TobiasVanDyk/Microdexed-Synth-Variations/i2cbackpack/address-jumpers.png

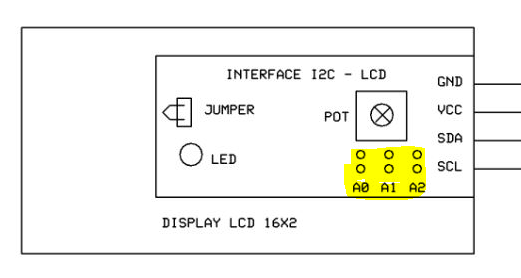
i2cbackpack/address-jumpers.png
