TobiasVanDyk/Microdexed-Synth-Variations/Microdexed2/images/mdt2.jpg

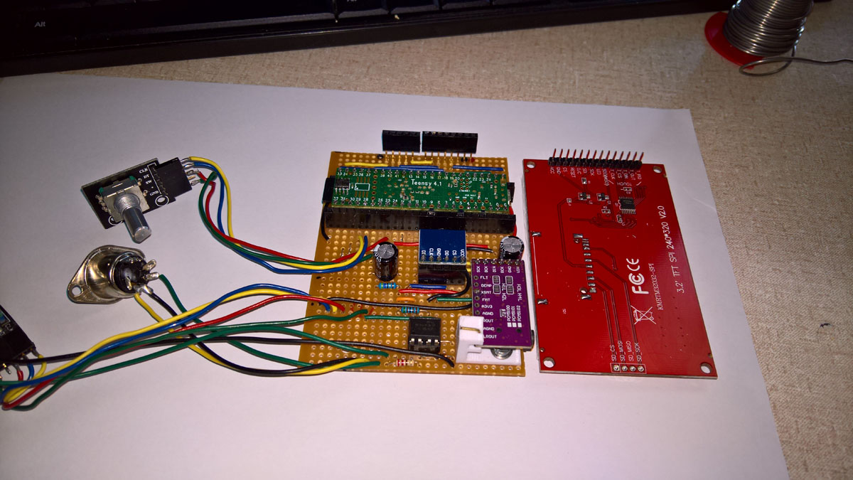
Microdexed2/images/mdt2.jpg
