TobiasVanDyk/Microdexed-Synth-Variations/Microdexed3/images/SDCard.png

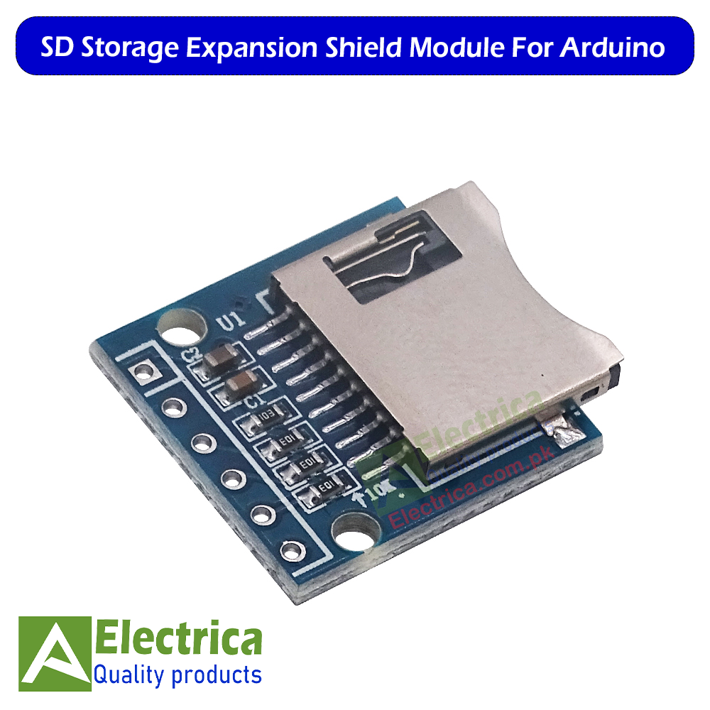
Microdexed3/images/SDCard.png
