TobiasVanDyk/Microdexed-Synth-Variations/Microdexed3/images/SDCardBack.png

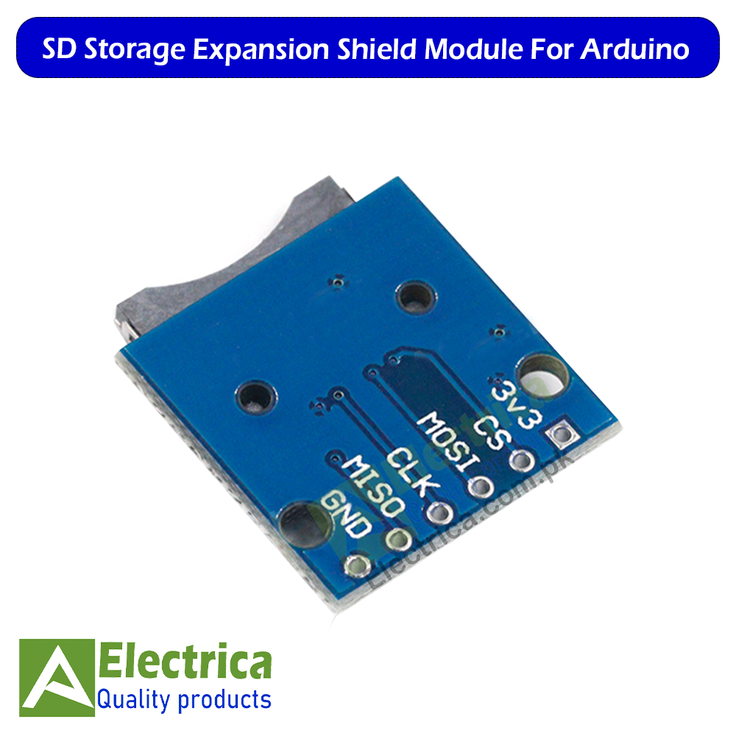
Microdexed3/images/SDCardBack.png
