TobiasVanDyk/Microdexed-Synth-Variations/Minidexed1/images/Pins.png

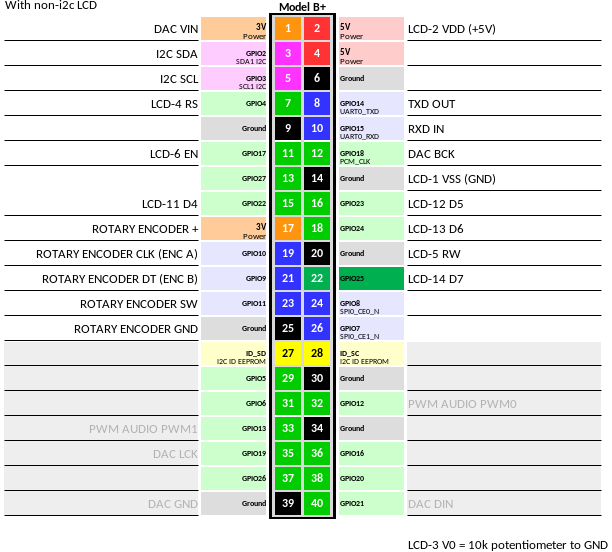
Minidexed1/images/Pins.png
