TobiasVanDyk/Microdexed-Synth-Variations/Minidexed2/Encoder.JPG

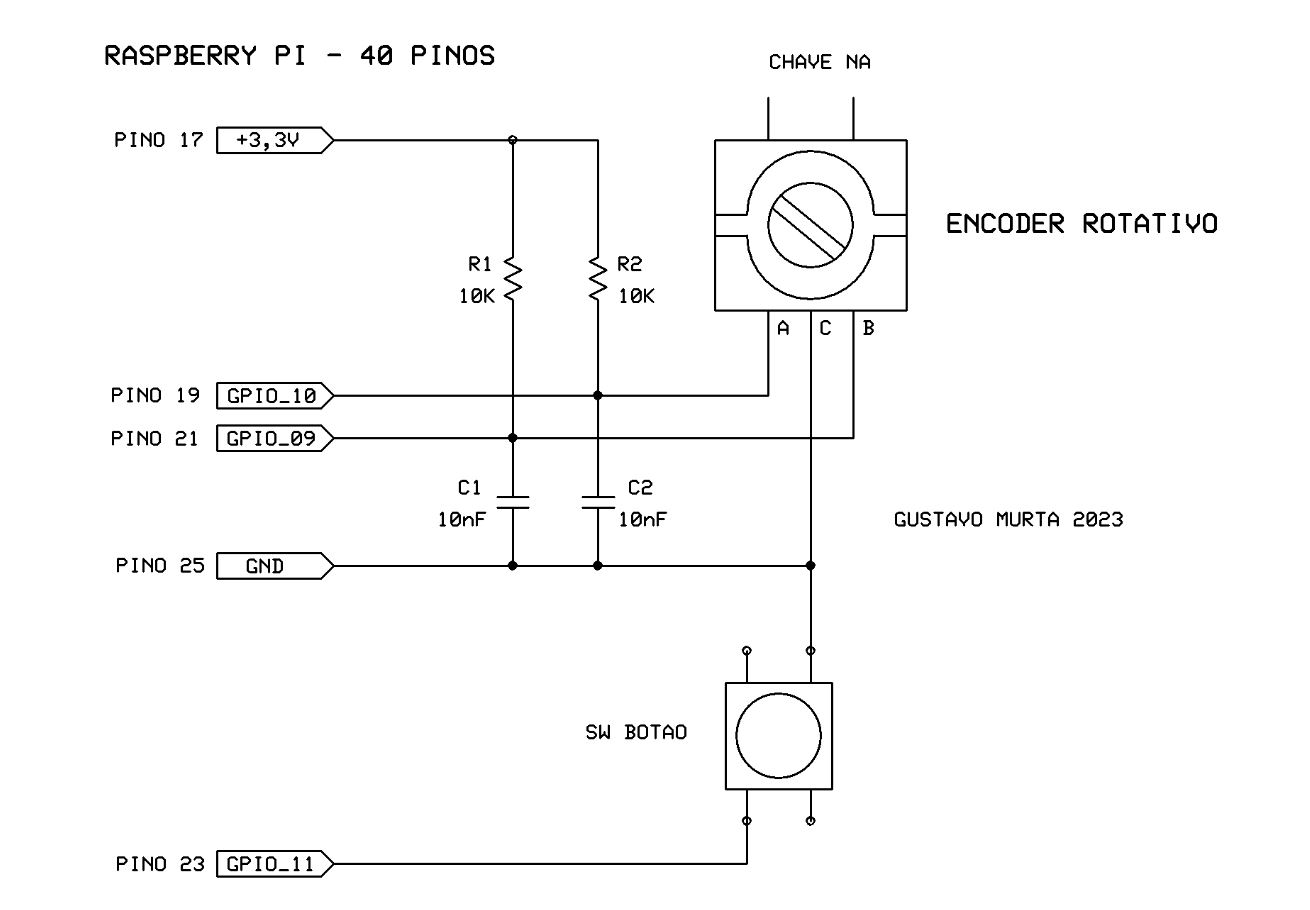
Minidexed2/Encoder.JPG
