TobiasVanDyk/Microdexed-Synth-Variations/Minidexed1/Minidexed-compile-WSL2-Win11/minidexed.ini

#
# minidexed.ini
#

# Sound device
SoundDevice=i2s
#SoundDevice=pwm
#SoundDevice=hdmi
SampleRate=48000
#ChunkSize=256
DACI2CAddress=0
ChannelsSwapped=0
# Engine Type ( 1=Modern ; 2=Mark I ; 3=OPL )
EngineType=1

# MIDI
MIDIBaudRate=31250
#MIDIThru=umidi1,ttyS1
IgnoreAllNotesOff=0
MIDIAutoVoiceDumpOnPC=1
HeaderlessSysExVoices=0
# Program Change enable
#   0 = Ignore all Program Change messages.
#   1 = Respond to Program Change messages.
MIDIRXProgramChange=1
# Program Change mode
#   0 = Only recognise Program Change 0-31.
#   1 = Support 0-127 across four consecutive banks.
# NB: Only relevant if PerformanceSelectChannel=0
ExpandPCAcrossBanks=1
# Program Change action:
#   0 = Program Change messages select voices on the channel associated with each TG.
#   1-16 = Program Change messages on this channel select performances.
#   >16 = Program Change messages on ANY channel select performances.
# NB: In performance mode, all Program Change messages on other channels are ignored.
PerformanceSelectChannel=0

# HD44780 LCD
LCDEnabled=1
LCDPinEnable=17
LCDPinRegisterSelect=4
LCDPinReadWrite=0
LCDPinData4=22
LCDPinData5=23
LCDPinData6=24
LCDPinData7=25
LCDI2CAddress=0x27

# SSD1306 LCD
# For a 128x32 display, set LCDColumns=20; LCDRows=2
# For a 128x64 display, set LCDColumns=20; LCDRows=4
SSD1306LCDI2CAddress=0x0
SSD1306LCDWidth=128
SSD1306LCDHeight=32
SSD1306LCDRotate=0
SSD1306LCDMirror=0

# Default is 16x2 display (e.g. HD44780)
LCDColumns=16
LCDRows=2

# GPIO Button Navigation
#  Any buttons set to 0 will be ignored
ButtonPinPrev=0
ButtonActionPrev=
ButtonPinNext=0
ButtonActionNext=
ButtonPinBack=11
ButtonActionBack=longpress
ButtonPinSelect=11
ButtonActionSelect=click
ButtonPinHome=11
ButtonActionHome=doubleclick
ButtonPinShortcut=11
# (Shortcut doesn't have an action)

# GPIO Program/TG Selection
#  Any buttons set to 0 will be ignored
ButtonPinPgmUp=0
ButtonActionPgmUp=
ButtonPinPgmDown=0
ButtonActionPgmDown=
ButtonPinTGUp=0
ButtonActionTGUp=
ButtonPinTGDown=0
ButtonActionTGDown=

# Timeouts in milliseconds for double click and long press
DoubleClickTimeout=400
LongPressTimeout=400

# MIDI Button Navigation
#  Specify MIDI CC to act as a button (0 = ununsed, so don't use CC 0)
#  NB: Off < 64 < ON
# CC channel: 0=OFF; 1-16 MIDI Ch; >16 Omni
# If MIDIButtonNotes>0 then treat MIDIButton numbers as MIDI
# Note numbers, triggered with NoteOn/NoteOff, not CC numbers.
MIDIButtonCh=0
MIDIButtonNotes=0
MIDIButtonPrev=0
MIDIButtonNext=0
MIDIButtonBack=0
MIDIButtonSelect=0
MIDIButtonHome=0
MIDIButtonPgmUp=0
MIDIButtonPgmDown=0
MIDIButtonTGUp=0
MIDIButtonTGDown=0

# KY-040 Rotary Encoder
EncoderEnabled=1
EncoderPinClock=10
EncoderPinData=9

# Debug
MIDIDumpEnabled=0
ProfileEnabled=0

# Performance
PerformanceSelectToLoad=1
