TobiasVanDyk/Microdexed-Synth-Variations/Microdexed3/MicroDexedTeensy41Dev/UI.hpp

/*
   MicroDexed

   MicroDexed is a port of the Dexed sound engine
   (https://github.com/asb2m10/dexed) for the Teensy-3.5/3.6/4.x with audio shield.
   Dexed ist heavily based on https://github.com/google/music-synthesizer-for-android

   (c)2018-2023 H. Wirtz <wirtz@parasitstudio.de>
   (c)2021-2022 H. Wirtz <wirtz@parasitstudio.de>, M. Koslowski <positionhigh@gmx.de>

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
   You should have received a copy of the GNU General Public License
   along with this program; if not, write to the Free Software Foundation,
   Inc., 51 Franklin Street, Fifth Floor, Boston, MA 02110-1301  USA
*/

#pragma once

#include "config.h"
#include <LCDMenuLib2.h>
#include <MD_REncoder.h>
#include <effect_modulated_delay.h>
#include <effect_stereo_mono.h>
#include <effect_mono_stereo.h>
#include <effect_platervbstereo.h>
#include <template_mixer.hpp>
#include "disp_plus.h"
#include "midi_devices.hpp"
#include "synth_dexed.h"
#include "synth_mda_epiano.h"
#include "drumset.h"
#include "dexed_sd.h"
#include <effect_stereo_panorama.h>
#if defined(USE_DELAY_8M)
#include <effect_delay_ext8.h>
#endif

#define _LCDML_DISP_cols LCD_cols
#define _LCDML_DISP_rows LCD_rows

#ifdef I2C_DISPLAY
#define _LCDML_DISP_cfg_cursor 0x7E  // cursor Symbol
#else
#define _LCDML_DISP_cfg_cursor 0x8d  // cursor Symbol
#endif
#define _LCDML_DISP_cfg_scrollbar 1  // enable a scrollbar

extern uint8_t midi_learn_mode;
extern uint8_t active_sample;

extern config_t configuration;
extern void set_volume(uint8_t v, uint8_t m);
extern bool load_sysex(uint8_t b, uint8_t v);
extern void generate_version_string(char* buffer, uint8_t len);
extern void _softRestart(void);
extern float midi_volume_transform(uint8_t midi_amp);
extern float volume_transform(float amp);
extern uint8_t selected_instance_id;
extern char receive_bank_filename[FILENAME_LEN];
extern void eeprom_update(void);

#if NUM_DRUMS > 0
#include "midinotes.h"
#include "drumset.h"
extern void get_sd_performance_name_json(uint8_t number, char* name, uint8_t len);
extern bool save_sd_performance_json(uint8_t p);
extern uint8_t drum_midi_channel;
uint8_t activesample = 0;
#endif

#ifdef SGTL5000_AUDIO_ENHANCE
#include "control_sgtl5000plus.h"
extern AudioControlSGTL5000Plus sgtl5000;
#else
extern AudioControlSGTL5000 sgtl5000;
#endif

extern AudioSynthDexed* MicroDexed[NUM_DEXED];

extern AudioSynthWaveform* chorus_modulator[NUM_DEXED];
extern AudioEffectModulatedDelay* modchorus[NUM_DEXED];
extern AudioMixer<2>* chorus_mixer[NUM_DEXED];
extern AudioMixer<2>* delay_fb_mixer[NUM_DEXED];
#if defined(USE_DELAY_8M)
extern AudioEffectDelayExternal8* delay_fx[NUM_DEXED];
#else
extern AudioEffectDelay* delay_fx[NUM_DEXED];
#endif
extern AudioMixer<2>* delay_mixer[NUM_DEXED];
extern AudioEffectMonoStereo* mono2stereo[NUM_DEXED];
extern AudioMixer<2> microdexed_peak_mixer;
extern AudioAnalyzePeak microdexed_peak;
extern AudioSynthEPiano ep;
extern AudioMixer<4> reverb_mixer_r;
extern AudioMixer<4> reverb_mixer_l;
extern AudioEffectPlateReverb reverb;
extern AudioEffectStereoPanorama ep_stereo_panorama;
extern AudioSynthWaveform ep_chorus_modulator;
#if MOD_FILTER_OUTPUT != MOD_NO_FILTER_OUTPUT
extern AudioFilterBiquad ep_modchorus_filter;
#endif
extern AudioEffectModulatedDelayStereo ep_modchorus;
extern AudioMixer<2> ep_chorus_mixer_r;
extern AudioMixer<2> ep_chorus_mixer_l;
extern AudioMixer<2> ep_delay_fb_mixer_r;
extern AudioMixer<2> ep_delay_fb_mixer_l;
extern AudioEffectDelay ep_delay_fx_r;
extern AudioEffectDelay ep_delay_fx_l;
extern AudioMixer<2> ep_delay_mixer_r;
extern AudioMixer<2> ep_delay_mixer_l;
extern AudioMixer<5> master_mixer_r;
extern AudioMixer<5> master_mixer_l;
extern AudioEffectStereoMono stereo2mono;
extern AudioAnalyzePeak master_peak_r;
extern AudioAnalyzePeak master_peak_l;

extern char sd_string[LCD_cols + 1];
extern char g_voice_name[NUM_DEXED][VOICE_NAME_LEN];
extern char g_bank_name[NUM_DEXED][BANK_NAME_LEN];
extern int perform_attack_mod[NUM_DEXED];
extern int perform_release_mod[NUM_DEXED];
extern const float midi_ticks_factor[10];
extern uint8_t midi_bpm;
extern bool save_sys_flag;
extern elapsedMillis save_sys;
extern bool save_sys_flag;
extern uint8_t midinote_old[NUM_DRUMSET_CONFIG];

/***********************************************************************
   GLOBAL
************************************************************************/
elapsedMillis back_from_volume;
uint8_t instance_num[8][8];
const char accepted_chars[] = " ABCDEFGHIJKLMNOPQRSTUVWXYZ0123456789-abcdefghijklmnopqrstuvwxyz";
//const char noteNames[12][3] = { "C", "C#", "D", "D#", "E", "F", "F#", "G", "G#", "A", "A#", "B" };
uint8_t active_perform_page = 1;
uint8_t orig_attack_values[2][7];
uint8_t orig_release_values[2][7];
int temp_int;
float temp_float;
bool ask_before_quit = false;

#ifdef I2C_DISPLAY
#include <LiquidCrystal_I2C.h>
Disp_Plus<LiquidCrystal_I2C> display(LCD_I2C_ADDRESS, _LCDML_DISP_cols, _LCDML_DISP_rows);
#endif

#ifdef U8X8_DISPLAY
#include <U8x8lib.h>
#ifdef U8X8_HAVE_HW_SPI
#include <SPI.h>
#endif
#ifdef U8X8_HAVE_HW_I2C
#include <Wire.h>
#endif
Disp_Plus<U8X8_DISPLAY_CLASS> lcd(/* cs=*/U8X8_CS_PIN, /* dc=*/U8X8_DC_PIN, /* reset=*/U8X8_RESET_PIN);
//Disp_Plus<U8X8_DISPLAY_CLASS> lcd(U8X8_PIN_NONE);
#endif

const uint8_t scroll_bar[5][8] = {
  { B10001, B10001, B10001, B10001, B10001, B10001, B10001, B10001 },  // scrollbar top
  { B11111, B11111, B10001, B10001, B10001, B10001, B10001, B10001 },  // scroll state 1
  { B10001, B10001, B11111, B11111, B10001, B10001, B10001, B10001 },  // scroll state 2
  { B10001, B10001, B10001, B10001, B11111, B11111, B10001, B10001 },  // scroll state 3
  { B10001, B10001, B10001, B10001, B10001, B10001, B11111, B11111 }   // scrollbar bottom
};

const uint8_t block_bar[5][8] = {
  { B10000, B10000, B10000, B10000, B10000, B10000, B10000, B10000 },
  { B11000, B11000, B11000, B11000, B11000, B11000, B11000, B11000 },
  { B11100, B11100, B11100, B11100, B11100, B11100, B11100, B11100 },
  { B11110, B11110, B11110, B11110, B11110, B11110, B11110, B11110 },
  { B11111, B11111, B11111, B11111, B11111, B11111, B11111, B11111 }
};

const uint8_t meter_bar[5][8] = {
  { B10000, B10000, B10000, B10000, B10000, B10000, B10000, B10000 },
  { B01000, B01000, B01000, B01000, B01000, B01000, B01000, B01000 },
  { B00100, B00100, B00100, B00100, B00100, B00100, B00100, B00100 },
  { B00010, B00010, B00010, B00010, B00010, B00010, B00010, B00010 },
  { B00001, B00001, B00001, B00001, B00001, B00001, B00001, B00001 }
};

const uint8_t special_chars[20][8] = {
  { B11111, B11011, B10011, B11011, B11011, B11011, B11011, B11111 },  //  [0] 1 small invers
  { B11111, B11011, B10101, B11101, B11011, B10111, B10001, B11111 },  //  [1] 2 small invers
  { B11111, B11011, B10011, B11011, B11011, B11011, B11011, B11111 },  //  [2] 1 OP invers
  { B11111, B11011, B10101, B11101, B11011, B10111, B10001, B11111 },  //  [3] 2 OP invers
  { B11111, B10001, B11101, B11011, B11101, B10101, B11011, B11111 },  //  [4] 3 OP invers
  { B11111, B10111, B10111, B10101, B10001, B11101, B11101, B11111 },  //  [5] 4 OP invers
  { B11111, B10001, B10111, B10011, B11101, B11101, B10011, B11111 },  //  [6] 5 OP invers
  { B11111, B11001, B10111, B10011, B10101, B10101, B11011, B11111 },  //  [7] 6 OP invers
  { B00000, B00000, B00000, B00000, B00000, B00000, B00000, B11111 },  //  [8] Level 1
  { B00000, B00000, B00000, B00000, B00000, B00000, B11111, B11111 },  //  [9] Level 2
  { B00000, B00000, B00000, B00000, B00000, B11111, B11111, B11111 },  // [10] Level 3
  { B00000, B00000, B00000, B00000, B11111, B11111, B11111, B11111 },  // [11] Level 4
  { B00000, B00000, B00000, B11111, B11111, B11111, B11111, B11111 },  // [12] Level 5
  { B00000, B00000, B11111, B11111, B11111, B11111, B11111, B11111 },  // [13] Level 6
  { B00000, B11111, B11111, B11111, B11111, B11111, B11111, B11111 },  // [14] Level 7
  { B11111, B11111, B11111, B11111, B11111, B11111, B11111, B11111 },  // [15] Level 8
  { B00100, B00110, B00101, B00101, B01101, B11101, B11100, B11000 },  // [16] Note
  { B01110, B10001, B10001, B01110, B00100, B00100, B00110, B00110 },  // [17] Disabled 2nd instance symbol
  { B11111, B10001, B10111, B10001, B10111, B10111, B10111, B11111 },  // [18] Favorites Icon
  { B11111, B10001, B10111, B10001, B10111, B10001, B11111, B00000 }   // [19] Edit Icon
};

enum { SCROLLBAR,
       BLOCKBAR,
       METERBAR
};
enum { ENC_R,
       ENC_L
};
enum { MENU_VOICE_BANK,
       MENU_VOICE_SOUND
};

void lcdml_menu_display(void);
void lcdml_menu_clear(void);
void lcdml_menu_control(void);
void UI_func_reverb_roomsize(uint8_t param);
void UI_func_reverb_damping(uint8_t param);
void UI_func_reverb_lowpass(uint8_t param);
void UI_func_reverb_lodamp(uint8_t param);
void UI_func_reverb_hidamp(uint8_t param);
void UI_func_reverb_diffusion(uint8_t param);
void UI_func_reverb_level(uint8_t param);
void UI_func_chorus_frequency(uint8_t param);
void UI_func_chorus_waveform(uint8_t param);
void UI_func_chorus_depth(uint8_t param);
void UI_func_chorus_level(uint8_t param);
void UI_func_delay_time(uint8_t param);
void UI_func_delay_feedback(uint8_t param);
void UI_func_delay_level(uint8_t param);
void UI_func_reverb_send(uint8_t param);
void UI_func_filter_cutoff(uint8_t param);
void UI_func_filter_resonance(uint8_t param);
void UI_func_drum_reverb_send(uint8_t param);
void UI_func_transpose(uint8_t param);
void UI_func_tune(uint8_t param);
void UI_func_midi_channel(uint8_t param);
void UI_func_lowest_note(uint8_t param);
void UI_func_highest_note(uint8_t param);
void UI_func_sound_intensity(uint8_t param);
void UI_func_panorama(uint8_t param);
void UI_func_stereo_mono(uint8_t param);
void UI_func_note_refresh(uint8_t param);
void UI_func_polyphony(uint8_t param);
void UI_func_mono_poly(uint8_t param);
void UI_func_pb_range(uint8_t param);
void UI_func_pb_step(uint8_t param);
void UI_func_mw_range(uint8_t param);
void UI_func_mw_assign(uint8_t param);
void UI_func_mw_mode(uint8_t param);
void UI_func_fc_range(uint8_t param);
void UI_func_fc_assign(uint8_t param);
void UI_func_fc_mode(uint8_t param);
void UI_func_bc_range(uint8_t param);
void UI_func_bc_assign(uint8_t param);
void UI_func_bc_mode(uint8_t param);
void UI_func_at_range(uint8_t param);
void UI_func_at_assign(uint8_t param);
void UI_func_at_mode(uint8_t param);
void UI_func_portamento_mode(uint8_t param);
void UI_func_portamento_glissando(uint8_t param);
void UI_func_portamento_time(uint8_t param);
void UI_handle_OP(uint8_t param);
void UI_func_information(uint8_t param);
void UI_func_set_performance_name(uint8_t param);
void UI_func_volume(uint8_t param);
void UI_func_smart_filter(uint8_t param);
void UI_func_load_performance(uint8_t param);
void UI_func_save_performance(uint8_t param);
void UI_func_save_voice(uint8_t param);
void UI_func_midi_soft_thru(uint8_t param);
void UI_func_velocity_level(uint8_t param);
void UI_func_engine(uint8_t param);
void UI_func_voice_select(uint8_t param);
void UI_func_sysex_send_voice(uint8_t param);
void UI_func_sysex_receive_bank(uint8_t param);
void UI_func_sysex_send_bank(uint8_t param);
void UI_func_eq_1(uint8_t param);
void UI_func_eq_2(uint8_t param);
void UI_func_eq_3(uint8_t param);
void UI_func_eq_4(uint8_t param);
void UI_func_eq_5(uint8_t param);
void UI_func_eq_6(uint8_t param);
void UI_func_eq_7(uint8_t param);
void UI_func_startup(uint8_t param);
void UI_function_not_enabled(void);
void UI_function_not_implemented(uint8_t param);
void UI_func_favorites(uint8_t param);
void UI_func_epiano_sound_intensity(uint8_t param);
void UI_func_epiano_panorama(uint8_t param);
void UI_func_epiano_decay(uint8_t param);
void UI_func_epiano_release(uint8_t param);
void UI_func_epiano_hardness(uint8_t param);
void UI_func_epiano_treble(uint8_t param);
void UI_func_epiano_stereo(uint8_t param);
void UI_func_epiano_tune(uint8_t param);
void UI_func_epiano_detune(uint8_t param);
void UI_func_epiano_pan_tremolo(uint8_t param);
void UI_func_epiano_pan_lfo(uint8_t param);
void UI_func_epiano_overdrive(uint8_t param);
void UI_func_epiano_reverb_send(uint8_t param);
void UI_func_epiano_midi_channel(uint8_t param);
void UI_func_epiano_lowest_note(uint8_t param);
void UI_func_epiano_highest_note(uint8_t param);
void UI_func_epiano_transpose(uint8_t param);
void UI_func_epiano_polyphony(uint8_t param);
void UI_func_epiano_velocity_sense(uint8_t param);
void UI_func_epiano_chorus_frequency(uint8_t param);
void UI_func_epiano_chorus_waveform(uint8_t param);
void UI_func_epiano_chorus_depth(uint8_t param);
void UI_func_epiano_chorus_level(uint8_t param);
void UI_func_drum_midi_channel(uint8_t param);
void UI_func_drum_main_volume(uint8_t param);
void UI_func_drum_vol_min_max(uint8_t param);
void UI_func_drum_pan(uint8_t param);
void UI_func_drum_pitch(uint8_t param);
void UI_func_drum_midi_note(uint8_t param);
void UI_update_instance_icons();
bool UI_select_name(uint8_t y, uint8_t x, char* edit_string, uint8_t len, bool init);
uint8_t search_accepted_char(uint8_t c);
void display_int(int16_t var, uint8_t size, bool zeros, bool brackets, bool sign);
void display_float(float var, uint8_t size_number, uint8_t size_fraction, bool zeros, bool brackets, bool sign);
void display_bar_int(const char* title, uint32_t value, float factor, int32_t min_value, int32_t max_value, uint8_t size, bool zeros, bool sign, bool init);
void display_bar_float(const char* title, float value, float factor, int32_t min_value, int32_t max_value, uint8_t size_number, uint8_t size_fraction, bool zeros, bool sign, bool init);
void display_meter_int(const char* title, uint32_t value, float factor, float offset, int32_t min_value, int32_t max_value, uint8_t size, bool zeros, bool sign, bool init);
void display_meter_float(const char* title, float value, float factor, float offset, int32_t min_value, int32_t max_value, uint8_t size_number, uint8_t size_fraction, bool zeros, bool sign, bool init);
void lcd_active_instance_number(uint8_t instance_id);
void lcd_OP_active_instance_number(uint8_t instance_id, uint8_t op);
void lcd_special_chars(uint8_t mode);
void string_trim(char* s);
void save_favorite(uint8_t b, uint8_t v, uint8_t instance_id);
void draw_favorite_icon(uint8_t b, uint8_t v, uint8_t instance_id);
bool check_favorite(uint8_t b, uint8_t v, uint8_t instance_id);
bool quick_check_favorites_in_bank(uint8_t b, uint8_t instance_id);
void locate_previous_non_favorite();
void locate_previous_favorite();
void locate_next_favorite();
void locate_next_non_favorite();
void locate_random_non_favorite();

char* basename(const char* filename);
char* strip_extension(char* filename);

// normal menu
LCDMenuLib2_menu LCDML_0(255, 0, 0, NULL, NULL);  // normal root menu element (do not change)
LCDMenuLib2 LCDML(LCDML_0, _LCDML_DISP_rows, _LCDML_DISP_cols, lcdml_menu_display, lcdml_menu_clear, lcdml_menu_control);

#include "UI.h"

int favsearcher = 0;

// create menu
LCDML_createMenu(_LCDML_DISP_cnt);

/***********************************************************************
   CONTROL
 ***********************************************************************/
class EncoderDirection {
public:
  EncoderDirection(void) {
    reset();
  }

  void reset(void) {
    button_short = false;
    button_long = false;
    button_pressed = false;
    left = false;
    right = false;
    up = false;
    down = false;
  }

  void ButtonShort(bool state) {
    button_short = state;
  }

  bool ButtonShort(void) {
    if (button_short == true) {
      button_short = false;
      return (true);
    }
    return (false);
  }

  void ButtonLong(bool state) {
    button_long = state;
  }

  bool ButtonLong(void) {
    if (button_long == true) {
      button_long = false;
      return (true);
    }
    return (false);
  }

  void ButtonPressed(bool state) {
    button_pressed = state;
  }

  bool ButtonPressed(void) {
    return (button_pressed);
  }

  void Left(bool state) {
    left = state;
  }

  bool Left(void) {
    if (left == true) {
      left = false;
      return (true);
    }
    return (false);
  }

  void Right(bool state) {
    right = state;
  }

  bool Right(void) {
    if (right == true) {
      right = false;
      return (true);
    }
    return (false);
  }

  void Up(bool state) {
    up = state;
  }

  bool Up(void) {
    if (up == true) {
      up = false;
      return (true);
    }
    return (false);
  }

  void Down(bool state) {
    down = state;
  }

  bool Down(void) {
    if (down == true) {
      down = false;
      return (true);
    }
    return (false);
  }

private:
  bool button_short;
  bool button_long;
  bool button_pressed;
  bool left;
  bool right;
  bool up;
  bool down;
};

MD_REncoder ENCODER[NUM_ENCODER] = { MD_REncoder(ENC_R_PIN_B, ENC_R_PIN_A), MD_REncoder(ENC_L_PIN_B, ENC_L_PIN_A) };
EncoderDirection encoderDir[NUM_ENCODER];

long g_LCDML_CONTROL_button_press_time[NUM_ENCODER] = { 0, 0 };
bool g_LCDML_CONTROL_button_prev[NUM_ENCODER] = { HIGH, HIGH };
uint8_t g_LCDML_CONTROL_prev[NUM_ENCODER] = { 0, 0 };
bool menu_init = true;

#ifdef U8X8_DISPLAY
const uint8_t* flipped_scroll_bar[5];
const uint8_t* flipped_block_bar[7];
const uint8_t* flipped_meter_bar[7];

uint8_t* rotTile(const uint8_t* tile) {
  uint8_t* newt = new uint8_t[8];
  for (int x = 0; x < 8; x++) {
    uint8_t newb = 0;
    for (int y = 0; y < 8; y++) {
      newb |= (tile[y] << x) & 0x80;
      newb >>= 1;
    }
    newt[x] = newb;
  }
  return newt;
}
#endif

FLASHMEM void setup_ui(void) {
  // LCD Begin
#ifdef I2C_DISPLAY
  display.init();
  display.backlight();
  display.clear();
  display.noCursor();
#else
  display.begin();
  display.clear();
  display.setFont(u8x8_font_amstrad_cpc_extended_f);
#endif
  display.setCursor(3, 0);
  display.print(F("MicroDexed"));
  display.setCursor(0, 1);
  display.print(F("(c)parasiTstudio"));

  lcd_special_chars(SCROLLBAR);
  // LCDMenuLib Setup
  LCDML_setup(_LCDML_DISP_cnt);
}

#ifdef DEBUG
FLASHMEM void setup_debug_message(void) {
  // LCD Begin
  display.clear();
  display.setCursor(1, 0);
  display.print(F("* DEBUG MODE *"));
  display.setCursor(1, 1);
  display.print(F("ENABLE CONSOLE"));
  delay(300);
  display.setCursor(1, 1);
  display.print(_LCDML_VERSION);
  display.print(F("  "));
}
#endif

/***********************************************************************
   MENU CONTROL
 ***********************************************************************/
uint8_t get_current_cursor_id(void) {
  LCDMenuLib2_menu* tmp;

  if ((tmp = LCDML.MENU_getCurrentObj()) != NULL)
    return (tmp->getChild(LCDML.MENU_getCursorPosAbs())->getID());
  else
    return (0);
}

void lcdml_menu_control(void) {
  // If something must init, put in in the setup condition
  if (LCDML.BT_setup()) {
    pinMode(BUT_R_PIN, INPUT_PULLUP);
    pinMode(BUT_L_PIN, INPUT_PULLUP);

    ENCODER[ENC_R].begin();
    ENCODER[ENC_L].begin();
  }

  if (back_from_volume > BACK_FROM_VOLUME_MS && LCDML.FUNC_getID() == LCDML.OTHER_getIDFromFunction(UI_func_volume)) {
    encoderDir[ENC_L].reset();
    encoderDir[ENC_R].reset();

    if (LCDML.MENU_getLastActiveFunctionID() < 0xff)
      LCDML.OTHER_jumpToID(LCDML.MENU_getLastActiveFunctionID());
    else
      LCDML.OTHER_setCursorToID(LCDML.MENU_getLastCursorPositionID());
    //LCDML.FUNC_goBackToMenu();
  }

  // Volatile Variables
  long g_LCDML_CONTROL_Encoder_position[NUM_ENCODER] = { ENCODER[ENC_R].read(), ENCODER[ENC_L].read() };
  bool button[NUM_ENCODER] = { bool(digitalRead(BUT_R_PIN)), bool(digitalRead(BUT_L_PIN)) };

  /************************************************************************************
    Basic encoder handling (from LCDMenuLib2)
   ************************************************************************************/

  // RIGHT
  if (g_LCDML_CONTROL_Encoder_position[ENC_R] <= -3) {
    if (!button[ENC_R]) {
      LCDML.BT_left();
#ifdef DEBUG
      Serial.println(F("ENC-R left"));
#endif
      encoderDir[ENC_R].Left(true);
      g_LCDML_CONTROL_button_prev[ENC_R] = LOW;
      g_LCDML_CONTROL_button_press_time[ENC_R] = -1;
    } else {
#ifdef DEBUG
      Serial.println(F("ENC-R down"));
#endif
      encoderDir[ENC_R].Down(true);
      LCDML.BT_down();
    }
    ENCODER[ENC_R].write(g_LCDML_CONTROL_Encoder_position[ENC_R] + 4);
  } else if (g_LCDML_CONTROL_Encoder_position[ENC_R] >= 3) {
    if (!button[ENC_R]) {
#ifdef DEBUG
      Serial.println(F("ENC-R right"));
#endif
      encoderDir[ENC_R].Right(true);
      LCDML.BT_right();
      g_LCDML_CONTROL_button_prev[ENC_R] = LOW;
      g_LCDML_CONTROL_button_press_time[ENC_R] = -1;
    } else {
#ifdef DEBUG
      Serial.println(F("ENC-R up"));
#endif
      encoderDir[ENC_R].Up(true);
      LCDML.BT_up();
    }
    ENCODER[ENC_R].write(g_LCDML_CONTROL_Encoder_position[ENC_R] - 4);
  } else {
    if (!button[ENC_R] && g_LCDML_CONTROL_button_prev[ENC_R])  //falling edge, button pressed
    {
      encoderDir[ENC_R].ButtonPressed(true);
      g_LCDML_CONTROL_button_prev[ENC_R] = LOW;
      g_LCDML_CONTROL_button_press_time[ENC_R] = millis();
    } else if (button[ENC_R] && !g_LCDML_CONTROL_button_prev[ENC_R])  //rising edge, button not active
    {
      encoderDir[ENC_R].ButtonPressed(false);
      g_LCDML_CONTROL_button_prev[ENC_R] = HIGH;

      if (g_LCDML_CONTROL_button_press_time[ENC_R] < 0) {
        g_LCDML_CONTROL_button_press_time[ENC_R] = millis();
        //Reset for left right action
      } else if ((millis() - g_LCDML_CONTROL_button_press_time[ENC_R]) >= LONG_BUTTON_PRESS) {
#ifdef DEBUG
        Serial.println(F("ENC-R long released"));
#endif
        //LCDML.BT_quit();
        encoderDir[ENC_R].ButtonLong(true);
      } else if ((millis() - g_LCDML_CONTROL_button_press_time[ENC_R]) >= BUT_DEBOUNCE_MS) {
#ifdef DEBUG
        Serial.println(F("ENC-R short"));
#endif
        encoderDir[ENC_R].ButtonShort(true);

        LCDML.BT_enter();
      }
    }
  }

  if (encoderDir[ENC_R].ButtonPressed() == true && (millis() - g_LCDML_CONTROL_button_press_time[ENC_R]) >= LONG_BUTTON_PRESS) {
#ifdef DEBUG
    Serial.println(F("ENC-R long recognized"));
#endif
    encoderDir[ENC_R].ButtonLong(true);

    if (LCDML.FUNC_getID() == LCDML.OTHER_getIDFromFunction(UI_func_voice_select)) {
      LCDML.BT_enter();
      LCDML.OTHER_updateFunc();
      LCDML.loop_menu();
      encoderDir[ENC_R].ButtonPressed(false);
      encoderDir[ENC_R].ButtonLong(false);
    } else {
      if (LCDML.FUNC_getID() < 0xff)
        LCDML.FUNC_setGBAToLastFunc();
      else
        LCDML.FUNC_setGBAToLastCursorPos();

      LCDML.OTHER_jumpToFunc(UI_func_voice_select);
      encoderDir[ENC_R].reset();
    }
  }

  // LEFT
  if (g_LCDML_CONTROL_Encoder_position[ENC_L] <= -3) {
    if (!button[ENC_L]) {
#ifdef DEBUG
      Serial.println(F("ENC-L left"));
#endif
      encoderDir[ENC_L].Left(true);
      LCDML.BT_left();
      g_LCDML_CONTROL_button_prev[ENC_L] = LOW;
      g_LCDML_CONTROL_button_press_time[ENC_L] = -1;
    } else {
#ifdef DEBUG
      Serial.println(F("ENC-L down"));
#endif
      encoderDir[ENC_L].Down(true);
      LCDML.BT_down();
      if (LCDML.FUNC_getID() != LCDML.OTHER_getIDFromFunction(UI_func_volume)) {
        LCDML.OTHER_jumpToFunc(UI_func_volume);
      }
    }
    ENCODER[ENC_L].write(g_LCDML_CONTROL_Encoder_position[ENC_L] + 4);
  } else if (g_LCDML_CONTROL_Encoder_position[ENC_L] >= 3) {
    if (!button[ENC_L]) {
#ifdef DEBUG
      Serial.println(F("ENC-L right"));
#endif
      encoderDir[ENC_L].Right(true);
      LCDML.BT_right();
      g_LCDML_CONTROL_button_prev[ENC_L] = LOW;
      g_LCDML_CONTROL_button_press_time[ENC_L] = -1;
    } else {
#ifdef DEBUG
      Serial.println(F("ENC-L up"));
#endif
      encoderDir[ENC_L].Up(true);
      LCDML.BT_up();
      if (LCDML.FUNC_getID() != LCDML.OTHER_getIDFromFunction(UI_func_volume)) {
        LCDML.OTHER_jumpToFunc(UI_func_volume);
      }
    }
    ENCODER[ENC_L].write(g_LCDML_CONTROL_Encoder_position[ENC_L] - 4);
  } else {
    if (!button[ENC_L] && g_LCDML_CONTROL_button_prev[ENC_L])  //falling edge, button pressed
    {
      encoderDir[ENC_L].ButtonPressed(true);
      g_LCDML_CONTROL_button_prev[ENC_L] = LOW;
      g_LCDML_CONTROL_button_press_time[ENC_L] = millis();
    } else if (button[ENC_L] && !g_LCDML_CONTROL_button_prev[ENC_L])  //rising edge, button not active
    {
      encoderDir[ENC_L].ButtonPressed(false);
      g_LCDML_CONTROL_button_prev[ENC_L] = HIGH;

      if (g_LCDML_CONTROL_button_press_time[ENC_L] < 0) {
        g_LCDML_CONTROL_button_press_time[ENC_L] = millis();
        //Reset for left right action
      } else if ((millis() - g_LCDML_CONTROL_button_press_time[ENC_L]) >= LONG_BUTTON_PRESS) {
#ifdef DEBUG
        Serial.println(F("ENC-L long released"));
#endif
        //encoderDir[ENC_L].ButtonLong(true);
        //LCDML.BT_quit();
      } else if ((millis() - g_LCDML_CONTROL_button_press_time[ENC_L]) >= BUT_DEBOUNCE_MS) {
        //LCDML.BT_enter();
#ifdef DEBUG
        Serial.println(F("ENC-L short"));
#endif
        encoderDir[ENC_L].ButtonShort(true);

        if ((LCDML.MENU_getLastActiveFunctionID() == 0xff && LCDML.MENU_getLastCursorPositionID() == 0) || menu_init == true) {
          LCDML.MENU_goRoot();
          menu_init = false;
        } else if (LCDML.FUNC_getID() == LCDML.OTHER_getIDFromFunction(UI_func_volume)) {
          encoderDir[ENC_L].reset();
          encoderDir[ENC_R].reset();

          if (LCDML.MENU_getLastActiveFunctionID() < 0xff)
            LCDML.OTHER_jumpToID(LCDML.MENU_getLastActiveFunctionID());
          else
            LCDML.OTHER_setCursorToID(LCDML.MENU_getLastCursorPositionID());
        } else if (LCDML.FUNC_getID() == LCDML.OTHER_getIDFromFunction(UI_func_drum_midi_note) && ask_before_quit == false) {
          ask_before_quit = true;
          Serial.printf("ask_before_quit = %d\n", ask_before_quit);
          encoderDir[ENC_L].reset();
          encoderDir[ENC_R].reset();
          LCDML.OTHER_updateFunc();
          LCDML.loop_menu();
        } else {
          ask_before_quit = false;
          Serial.printf("ask_before_quit = %d\n", ask_before_quit);
          LCDML.BT_quit();
        }
      }
    }
  }

  if (encoderDir[ENC_L].ButtonPressed() == true && (millis() - g_LCDML_CONTROL_button_press_time[ENC_L]) >= LONG_BUTTON_PRESS) {
#ifdef DEBUG
    Serial.println(F("ENC-L long recognized"));
#endif

    // when in Voice select Menu, long left-press sets/unsets favorite
    if (LCDML.FUNC_getID() == LCDML.OTHER_getIDFromFunction(UI_func_voice_select))
      save_favorite(configuration.dexed[selected_instance_id].bank, configuration.dexed[selected_instance_id].voice, selected_instance_id);

    //for (uint8_t i = 0; i < NUM_DEXED; i++)
    //  MicroDexed[i]->panic();

    encoderDir[ENC_L].reset();
    encoderDir[ENC_R].reset();
  }
}

/***********************************************************************
   MENU DISPLAY
 ***********************************************************************/
void lcdml_menu_clear(void) {
  display.clear();
  display.setCursor(0, 0);
}

void lcdml_menu_display(void) {
  // update content
  // ***************
  if (LCDML.DISP_checkMenuUpdate()) {
    // clear menu
    // ***************
    LCDML.DISP_clear();

    // declaration of some variables
    // ***************
    // content variable
    char content_text[_LCDML_DISP_cols];  // save the content text of every menu element
    // menu element object
    LCDMenuLib2_menu* tmp;
    // some limit values
    uint8_t i = LCDML.MENU_getScroll();
    uint8_t maxi = _LCDML_DISP_rows + i;
    uint8_t n = 0;

    // check if this element has children
    if ((tmp = LCDML.MENU_getDisplayedObj()) != NULL) {
      // loop to display lines
      do {
        // check if a menu element has a condition and if the condition be true
        if (tmp->checkCondition()) {
          // check the type off a menu element
          if (tmp->checkType_menu() == true) {
            // display normal content
            LCDML_getContent(content_text, tmp->getID());
            display.setCursor(1, n);
            display.print(content_text);
          } else {
            if (tmp->checkType_dynParam()) {
              tmp->callback(n);
            }
          }
          // increment some values
          i++;
          n++;
        }
        // try to go to the next sibling and check the number of displayed rows
      } while (((tmp = tmp->getSibling(1)) != NULL) && (i < maxi));
    }
  }

  if (LCDML.DISP_checkMenuCursorUpdate()) {
    // init vars
    uint8_t n_max = (LCDML.MENU_getChilds() >= _LCDML_DISP_rows) ? _LCDML_DISP_rows : (LCDML.MENU_getChilds());
    uint8_t scrollbar_min = 0;
    uint8_t scrollbar_max = LCDML.MENU_getChilds();
    uint8_t scrollbar_cur_pos = LCDML.MENU_getCursorPosAbs();
    uint8_t scroll_pos = ((1. * n_max * _LCDML_DISP_rows) / (scrollbar_max - 1) * scrollbar_cur_pos);

    // display rows
    for (uint8_t n = 0; n < n_max; n++) {
      //set cursor
      display.setCursor(0, n);

      //set cursor char
      if (n == LCDML.MENU_getCursorPos()) {
        display.write(_LCDML_DISP_cfg_cursor);
      } else {
        display.write(' ');
      }

      // delete or reset scrollbar
      if (_LCDML_DISP_cfg_scrollbar == 1) {
        if (scrollbar_max > n_max) {
#ifdef I2C_DISPLAY
          display.setCursor((_LCDML_DISP_cols - 1), n);
          display.write((uint8_t)0);
#else
          display.drawTile((_LCDML_DISP_cols - 1), n, 1, flipped_scroll_bar[0]);
          display.setCursor((_LCDML_DISP_cols), n + 1);
#endif
        } else {
          display.setCursor((_LCDML_DISP_cols - 1), n);
          display.print(F(" "));
        }
      }
    }

    // display scrollbar
    if (_LCDML_DISP_cfg_scrollbar == 1) {
      if (scrollbar_max > n_max) {
        //set scroll position
        if (scrollbar_cur_pos == scrollbar_min) {
          // min pos
#ifdef I2C_DISPLAY
          display.setCursor((_LCDML_DISP_cols - 1), 0);
          display.write((uint8_t)1);
#else
          display.drawTile((_LCDML_DISP_cols - 1), 0, 1, flipped_scroll_bar[1]);
          display.setCursor((_LCDML_DISP_cols), 1);
#endif
        } else if (scrollbar_cur_pos == (scrollbar_max - 1)) {
          // max pos
#ifdef I2C_DISPLAY
          display.setCursor((_LCDML_DISP_cols - 1), (n_max - 1));
          display.write((uint8_t)4);
#else
          display.drawTile((_LCDML_DISP_cols - 1), (n_max - 1), 1, flipped_scroll_bar[4]);
          display.setCursor((_LCDML_DISP_cols), (n_max));
#endif
        } else {
          // between
#ifdef I2C_DISPLAY
          display.setCursor((_LCDML_DISP_cols - 1), scroll_pos / n_max);
          display.write((uint8_t)(scroll_pos % n_max) + 1);
#else
          display.drawTile((_LCDML_DISP_cols - 1), scroll_pos / n_max, 1, flipped_scroll_bar[(scroll_pos % n_max) + 1]);
          display.setCursor((_LCDML_DISP_cols), (scroll_pos / n_max) + 1);
#endif
        }
      }
    }
  }
}

//####################################################################################################################################################################################################

/***********************************************************************
   MENU
 ***********************************************************************/

void UI_func_reverb_roomsize(uint8_t param) {
  if (LCDML.FUNC_setup())  // ****** SETUP *********
  {
    encoderDir[ENC_R].reset();

    lcd_special_chars(BLOCKBAR);
    display_bar_int("Reverb Room", configuration.fx.reverb_roomsize, 1.0, REVERB_ROOMSIZE_MIN, REVERB_ROOMSIZE_MAX, 3, false, false, true);
  }

  if (LCDML.FUNC_loop())  // ****** LOOP *********
  {
    if ((LCDML.BT_checkDown() && encoderDir[ENC_R].Down()) || (LCDML.BT_checkUp() && encoderDir[ENC_R].Up())) {
      if (LCDML.BT_checkDown())
        configuration.fx.reverb_roomsize = constrain(configuration.fx.reverb_roomsize + ENCODER[ENC_R].speed(), REVERB_ROOMSIZE_MIN, REVERB_ROOMSIZE_MAX);
      else if (LCDML.BT_checkUp())
        configuration.fx.reverb_roomsize = constrain(configuration.fx.reverb_roomsize - ENCODER[ENC_R].speed(), REVERB_ROOMSIZE_MIN, REVERB_ROOMSIZE_MAX);
    }
    display_bar_int("Reverb Room", configuration.fx.reverb_roomsize, 1.0, REVERB_ROOMSIZE_MIN, REVERB_ROOMSIZE_MAX, 3, false, false, false);

    reverb.size(mapfloat(configuration.fx.reverb_roomsize, REVERB_ROOMSIZE_MIN, REVERB_ROOMSIZE_MAX, 0.0, 1.0));
  }

  if (LCDML.FUNC_close())  // ****** STABLE END *********
  {
    lcd_special_chars(SCROLLBAR);
    encoderDir[ENC_R].reset();
  }
}

void UI_func_reverb_lowpass(uint8_t param) {
  if (LCDML.FUNC_setup())  // ****** SETUP *********
  {
    encoderDir[ENC_R].reset();

    lcd_special_chars(BLOCKBAR);
    display_bar_int("Reverb Lowpass", configuration.fx.reverb_lowpass, 1.0, REVERB_LOWPASS_MIN, REVERB_LOWPASS_MAX, 3, false, false, true);
  }

  if (LCDML.FUNC_loop())  // ****** LOOP *********
  {
    if ((LCDML.BT_checkDown() && encoderDir[ENC_R].Down()) || (LCDML.BT_checkUp() && encoderDir[ENC_R].Up())) {
      if (LCDML.BT_checkDown())
        configuration.fx.reverb_lowpass = constrain(configuration.fx.reverb_lowpass + ENCODER[ENC_R].speed(), REVERB_LOWPASS_MIN, REVERB_LOWPASS_MAX);
      else if (LCDML.BT_checkUp())
        configuration.fx.reverb_lowpass = constrain(configuration.fx.reverb_lowpass - ENCODER[ENC_R].speed(), REVERB_LOWPASS_MIN, REVERB_LOWPASS_MAX);
    }

    display_bar_int("Reverb Lowpass", configuration.fx.reverb_lowpass, 1.0, REVERB_LOWPASS_MIN, REVERB_LOWPASS_MAX, 3, false, false, false);

    reverb.lowpass(mapfloat(configuration.fx.reverb_lowpass, REVERB_LOWPASS_MIN, REVERB_LOWPASS_MAX, 0.0, 1.0));
  }

  if (LCDML.FUNC_close())  // ****** STABLE END *********
  {
    lcd_special_chars(SCROLLBAR);
    encoderDir[ENC_R].reset();
  }
}

void UI_func_reverb_lodamp(uint8_t param) {
  if (LCDML.FUNC_setup())  // ****** SETUP *********
  {
    encoderDir[ENC_R].reset();

    lcd_special_chars(BLOCKBAR);
    display_bar_int("Reverb Lodamp.", configuration.fx.reverb_lodamp, 1.0, REVERB_LODAMP_MIN, REVERB_LODAMP_MAX, 3, false, false, true);
  }

  if (LCDML.FUNC_loop())  // ****** LOOP *********
  {
    if ((LCDML.BT_checkDown() && encoderDir[ENC_R].Down()) || (LCDML.BT_checkUp() && encoderDir[ENC_R].Up())) {
      if (LCDML.BT_checkDown())
        configuration.fx.reverb_lodamp = constrain(configuration.fx.reverb_lodamp + ENCODER[ENC_R].speed(), REVERB_LODAMP_MIN, REVERB_LODAMP_MAX);
      else if (LCDML.BT_checkUp())
        configuration.fx.reverb_lodamp = constrain(configuration.fx.reverb_lodamp - ENCODER[ENC_R].speed(), REVERB_LODAMP_MIN, REVERB_LODAMP_MAX);
    }

    display_bar_int("Reverb Lodamp.", configuration.fx.reverb_lodamp, 1.0, REVERB_LODAMP_MIN, REVERB_LODAMP_MAX, 3, false, false, false);

    reverb.lodamp(mapfloat(configuration.fx.reverb_lodamp, REVERB_LODAMP_MIN, REVERB_LODAMP_MAX, 0.0, 1.0));
  }

  if (LCDML.FUNC_close())  // ****** STABLE END *********
  {
    lcd_special_chars(SCROLLBAR);
    encoderDir[ENC_R].reset();
  }
}

void UI_func_reverb_hidamp(uint8_t param) {
  if (LCDML.FUNC_setup())  // ****** SETUP *********
  {
    encoderDir[ENC_R].reset();

    lcd_special_chars(BLOCKBAR);
    display_bar_int("Reverb Hidamp.", configuration.fx.reverb_hidamp, 1.0, REVERB_HIDAMP_MIN, REVERB_HIDAMP_MAX, 3, false, false, true);
  }

  if (LCDML.FUNC_loop())  // ****** LOOP *********
  {
    if ((LCDML.BT_checkDown() && encoderDir[ENC_R].Down()) || (LCDML.BT_checkUp() && encoderDir[ENC_R].Up())) {
      if (LCDML.BT_checkDown())
        configuration.fx.reverb_hidamp = constrain(configuration.fx.reverb_hidamp + ENCODER[ENC_R].speed(), REVERB_HIDAMP_MIN, REVERB_HIDAMP_MAX);
      else if (LCDML.BT_checkUp())
        configuration.fx.reverb_hidamp = constrain(configuration.fx.reverb_hidamp - ENCODER[ENC_R].speed(), REVERB_HIDAMP_MIN, REVERB_HIDAMP_MAX);
    }

    display_bar_int("Reverb Hidamp.", configuration.fx.reverb_hidamp, 1.0, REVERB_HIDAMP_MIN, REVERB_HIDAMP_MAX, 3, false, false, false);

    reverb.hidamp(mapfloat(configuration.fx.reverb_hidamp, REVERB_HIDAMP_MIN, REVERB_HIDAMP_MAX, 0.0, 1.0));
  }

  if (LCDML.FUNC_close())  // ****** STABLE END *********
  {
    lcd_special_chars(SCROLLBAR);
    encoderDir[ENC_R].reset();
  }
}

void UI_func_reverb_diffusion(uint8_t param) {
  if (LCDML.FUNC_setup())  // ****** SETUP *********
  {
    encoderDir[ENC_R].reset();

    lcd_special_chars(BLOCKBAR);
    display_bar_int("Reverb Diff.", configuration.fx.reverb_diffusion, 1.0, REVERB_DIFFUSION_MIN, REVERB_DIFFUSION_MAX, 3, false, false, true);
  }

  if (LCDML.FUNC_loop())  // ****** LOOP *********
  {
    if ((LCDML.BT_checkDown() && encoderDir[ENC_R].Down()) || (LCDML.BT_checkUp() && encoderDir[ENC_R].Up())) {
      if (LCDML.BT_checkDown())
        configuration.fx.reverb_diffusion = constrain(configuration.fx.reverb_diffusion + ENCODER[ENC_R].speed(), REVERB_DIFFUSION_MIN, REVERB_DIFFUSION_MAX);
      else if (LCDML.BT_checkUp())
        configuration.fx.reverb_diffusion = constrain(configuration.fx.reverb_diffusion - ENCODER[ENC_R].speed(), REVERB_DIFFUSION_MIN, REVERB_DIFFUSION_MAX);
    }

    display_bar_int("Reverb Diff.", configuration.fx.reverb_diffusion, 1.0, REVERB_DIFFUSION_MIN, REVERB_DIFFUSION_MAX, 3, false, false, false);

    reverb.diffusion(mapfloat(configuration.fx.reverb_diffusion, REVERB_DIFFUSION_MIN, REVERB_DIFFUSION_MAX, 0.0, 1.0));
  }

  if (LCDML.FUNC_close())  // ****** STABLE END *********
  {
    lcd_special_chars(SCROLLBAR);
    encoderDir[ENC_R].reset();
  }
}

void UI_func_reverb_level(uint8_t param) {
  if (LCDML.FUNC_setup())  // ****** SETUP *********
  {
    encoderDir[ENC_R].reset();

    lcd_special_chars(BLOCKBAR);
    display_bar_int("Reverb Level", configuration.fx.reverb_level, 1.0, REVERB_LEVEL_MIN, REVERB_LEVEL_MAX, 3, false, false, true);
  }

  if (LCDML.FUNC_loop())  // ****** LOOP *********
  {
    if ((LCDML.BT_checkDown() && encoderDir[ENC_R].Down()) || (LCDML.BT_checkUp() && encoderDir[ENC_R].Up())) {
      if (LCDML.BT_checkDown())
        configuration.fx.reverb_level = constrain(configuration.fx.reverb_level + ENCODER[ENC_R].speed(), REVERB_LEVEL_MIN, REVERB_LEVEL_MAX);
      else if (LCDML.BT_checkUp())
        configuration.fx.reverb_level = constrain(configuration.fx.reverb_level - ENCODER[ENC_R].speed(), REVERB_LEVEL_MIN, REVERB_LEVEL_MAX);
    }

    display_bar_int("Reverb Level", configuration.fx.reverb_level, 1.0, REVERB_LEVEL_MIN, REVERB_LEVEL_MAX, 3, false, false, true);

    //master_mixer_r.gain(MASTER_MIX_CH_REVERB, pseudo_log_curve(mapfloat(configuration.fx.reverb_level, REVERB_LEVEL_MIN, REVERB_LEVEL_MAX, 0.0, 1.0)));
    //master_mixer_l.gain(MASTER_MIX_CH_REVERB, pseudo_log_curve(mapfloat(configuration.fx.reverb_level, REVERB_LEVEL_MIN, REVERB_LEVEL_MAX, 0.0, 1.0)));
    master_mixer_r.gain(MASTER_MIX_CH_REVERB, volume_transform(mapfloat(configuration.fx.reverb_level, REVERB_LEVEL_MIN, REVERB_LEVEL_MAX, 0.0, VOL_MAX_FLOAT)));
    master_mixer_l.gain(MASTER_MIX_CH_REVERB, volume_transform(mapfloat(configuration.fx.reverb_level, REVERB_LEVEL_MIN, REVERB_LEVEL_MAX, 0.0, VOL_MAX_FLOAT)));
  }

  if (LCDML.FUNC_close())  // ****** STABLE END *********
  {
    lcd_special_chars(SCROLLBAR);
    encoderDir[ENC_R].reset();
  }
}

void UI_func_chorus_frequency(uint8_t param) {
  if (LCDML.FUNC_setup())  // ****** SETUP *********
  {
    encoderDir[ENC_R].reset();

    lcd_special_chars(BLOCKBAR);
    display_bar_float("Chorus Frq.", configuration.fx.chorus_frequency[selected_instance_id], 0.1, CHORUS_FREQUENCY_MIN, CHORUS_FREQUENCY_MAX, 2, 1, false, false, true);

    lcd_active_instance_number(selected_instance_id);
    UI_update_instance_icons();
  }

  if (LCDML.FUNC_loop())  // ****** LOOP *********
  {
    if ((LCDML.BT_checkDown() && encoderDir[ENC_R].Down()) || (LCDML.BT_checkUp() && encoderDir[ENC_R].Up()) || (LCDML.BT_checkEnter() && encoderDir[ENC_R].ButtonShort())) {
      if (LCDML.BT_checkDown())
        configuration.fx.chorus_frequency[selected_instance_id] = constrain(configuration.fx.chorus_frequency[selected_instance_id] + ENCODER[ENC_R].speed(), CHORUS_FREQUENCY_MIN, CHORUS_FREQUENCY_MAX);
      else if (LCDML.BT_checkUp())
        configuration.fx.chorus_frequency[selected_instance_id] = constrain(configuration.fx.chorus_frequency[selected_instance_id] - ENCODER[ENC_R].speed(), CHORUS_FREQUENCY_MIN, CHORUS_FREQUENCY_MAX);
#if NUM_DEXED > 1
      else if (LCDML.BT_checkEnter()) {
        selected_instance_id = !selected_instance_id;
        lcd_active_instance_number(selected_instance_id);
        UI_update_instance_icons();
      }
#endif
    }
    display_bar_float("Chorus Frq.", configuration.fx.chorus_frequency[selected_instance_id], 0.1, CHORUS_FREQUENCY_MIN, CHORUS_FREQUENCY_MAX, 2, 1, false, false, false);

    chorus_modulator[selected_instance_id]->frequency(configuration.fx.chorus_frequency[selected_instance_id] / 10.0);
  }

  if (LCDML.FUNC_close())  // ****** STABLE END *********
  {
    lcd_special_chars(SCROLLBAR);
    encoderDir[ENC_R].reset();
  }
}

void UI_func_chorus_waveform(uint8_t param) {
  if (LCDML.FUNC_setup())  // ****** SETUP *********
  {
    encoderDir[ENC_R].reset();

    display.setCursor(0, 0);
    display.print(F("Chorus Wavefrm"));

    lcd_active_instance_number(selected_instance_id);
    UI_update_instance_icons();
  }

  if (LCDML.FUNC_loop())  // ****** LOOP *********
  {
    if (LCDML.BT_checkDown() && encoderDir[ENC_R].Down())
      configuration.fx.chorus_waveform[selected_instance_id] = constrain(configuration.fx.chorus_waveform[selected_instance_id] + 1, CHORUS_WAVEFORM_MIN, CHORUS_WAVEFORM_MAX);
    else if (LCDML.BT_checkUp() && encoderDir[ENC_R].Up())
      configuration.fx.chorus_waveform[selected_instance_id] = constrain(configuration.fx.chorus_waveform[selected_instance_id] - 1, CHORUS_WAVEFORM_MIN, CHORUS_WAVEFORM_MAX);
#if NUM_DEXED > 1
    else if (LCDML.BT_checkEnter() && encoderDir[ENC_R].ButtonShort()) {
      selected_instance_id = !selected_instance_id;
      lcd_active_instance_number(selected_instance_id);
      UI_update_instance_icons();
    }
#endif

    display.setCursor(0, 1);
    switch (configuration.fx.chorus_waveform[selected_instance_id]) {
      case 0:
        chorus_modulator[selected_instance_id]->begin(WAVEFORM_TRIANGLE);
        display.print(F("[TRIANGLE]"));
        break;
      case 1:
        chorus_modulator[selected_instance_id]->begin(WAVEFORM_SINE);
        display.print(F("[SINE    ]"));
        break;
      default:
        chorus_modulator[selected_instance_id]->begin(WAVEFORM_TRIANGLE);
        display.print(F("[TRIANGLE]"));
        break;
    }
  }

  if (LCDML.FUNC_close())  // ****** STABLE END *********
  {
    lcd_special_chars(SCROLLBAR);
    encoderDir[ENC_R].reset();
  }
}

void UI_func_chorus_depth(uint8_t param) {
  if (LCDML.FUNC_setup())  // ****** SETUP *********
  {
    encoderDir[ENC_R].reset();

    lcd_special_chars(BLOCKBAR);
    display_bar_int("Chorus Dpt.", configuration.fx.chorus_depth[selected_instance_id], 1.0, CHORUS_DEPTH_MIN, CHORUS_DEPTH_MAX, 3, false, false, true);

    lcd_active_instance_number(selected_instance_id);
    UI_update_instance_icons();
  }

  if (LCDML.FUNC_loop())  // ****** LOOP *********
  {
    if ((LCDML.BT_checkDown() && encoderDir[ENC_R].Down()) || (LCDML.BT_checkUp() && encoderDir[ENC_R].Up()) || (LCDML.BT_checkEnter() && encoderDir[ENC_R].ButtonShort())) {
      if (LCDML.BT_checkDown())
        configuration.fx.chorus_depth[selected_instance_id] = constrain(configuration.fx.chorus_depth[selected_instance_id] + ENCODER[ENC_R].speed(), CHORUS_DEPTH_MIN, CHORUS_DEPTH_MAX);
      else if (LCDML.BT_checkUp())
        configuration.fx.chorus_depth[selected_instance_id] = constrain(configuration.fx.chorus_depth[selected_instance_id] - ENCODER[ENC_R].speed(), CHORUS_DEPTH_MIN, CHORUS_DEPTH_MAX);
#if NUM_DEXED > 1
      else if (LCDML.BT_checkEnter()) {
        selected_instance_id = !selected_instance_id;
        lcd_active_instance_number(selected_instance_id);
        UI_update_instance_icons();
      }
#endif
    }

    display_bar_int("Chorus Dpt.", configuration.fx.chorus_depth[selected_instance_id], 1.0, CHORUS_DEPTH_MIN, CHORUS_DEPTH_MAX, 3, false, false, false);

    chorus_modulator[selected_instance_id]->amplitude(configuration.fx.chorus_depth[selected_instance_id] / 100.0);
  }

  if (LCDML.FUNC_close())  // ****** STABLE END *********
  {
    lcd_special_chars(SCROLLBAR);
    encoderDir[ENC_R].reset();
  }
}

void UI_func_chorus_level(uint8_t param) {
  if (LCDML.FUNC_setup())  // ****** SETUP *********
  {
    encoderDir[ENC_R].reset();

    lcd_special_chars(BLOCKBAR);
    display_bar_int("Chorus Lvl.", configuration.fx.chorus_level[selected_instance_id], 1.0, CHORUS_LEVEL_MIN, CHORUS_LEVEL_MAX, 3, false, false, true);

    lcd_active_instance_number(selected_instance_id);
    UI_update_instance_icons();
  }

  if (LCDML.FUNC_loop())  // ****** LOOP *********
  {
    if ((LCDML.BT_checkDown() && encoderDir[ENC_R].Down()) || (LCDML.BT_checkUp() && encoderDir[ENC_R].Up()) || (LCDML.BT_checkEnter() && encoderDir[ENC_R].ButtonShort())) {
      if (LCDML.BT_checkDown()) {
        configuration.fx.chorus_level[selected_instance_id] = constrain(configuration.fx.chorus_level[selected_instance_id] + ENCODER[ENC_R].speed(), CHORUS_LEVEL_MIN, CHORUS_LEVEL_MAX);
        MD_sendControlChange(configuration.dexed[selected_instance_id].midi_channel, 93, configuration.fx.chorus_level[selected_instance_id]);
      } else if (LCDML.BT_checkUp()) {
        configuration.fx.chorus_level[selected_instance_id] = constrain(configuration.fx.chorus_level[selected_instance_id] - ENCODER[ENC_R].speed(), CHORUS_LEVEL_MIN, CHORUS_LEVEL_MAX);
        MD_sendControlChange(configuration.dexed[selected_instance_id].midi_channel, 93, configuration.fx.chorus_level[selected_instance_id]);
      }
#if NUM_DEXED > 1
      else if (LCDML.BT_checkEnter()) {
        selected_instance_id = !selected_instance_id;
        lcd_active_instance_number(selected_instance_id);
        UI_update_instance_icons();
      }
#endif
    }

    display_bar_int("Chorus Lvl.", configuration.fx.chorus_level[selected_instance_id], 1.0, CHORUS_LEVEL_MIN, CHORUS_LEVEL_MAX, 3, false, false, false);

    //chorus_mixer[selected_instance_id]->gain(0, pseudo_log_curve(1.0 - mapfloat(configuration.fx.chorus_level[selected_instance_id], CHORUS_LEVEL_MIN, CHORUS_LEVEL_MAX, 0.0, 0.5)));
    //chorus_mixer[selected_instance_id]->gain(1, pseudo_log_curve(mapfloat(configuration.fx.chorus_level[selected_instance_id], CHORUS_LEVEL_MIN, CHORUS_LEVEL_MAX, 0.0, 0.5)));
    chorus_mixer[selected_instance_id]->gain(0, 1.0 - mapfloat(configuration.fx.chorus_level[selected_instance_id], CHORUS_LEVEL_MIN, CHORUS_LEVEL_MAX, 0.0, 0.5));
    //chorus_mixer[selected_instance_id]->gain(1, mapfloat(configuration.fx.chorus_level[selected_instance_id], CHORUS_LEVEL_MIN, CHORUS_LEVEL_MAX, 0.0, 0.5));
  }

  if (LCDML.FUNC_close())  // ****** STABLE END *********
  {
    lcd_special_chars(SCROLLBAR);
    encoderDir[ENC_R].reset();
  }
}

void UI_func_delay_time(uint8_t param) {
  if (LCDML.FUNC_setup())  // ****** SETUP *********
  {
    encoderDir[ENC_R].reset();

    lcd_special_chars(BLOCKBAR);

#if DELAY_TIME_MAX >= 1000
    display_bar_int("Delay Time", configuration.fx.delay_time[selected_instance_id], 10.0, DELAY_TIME_MIN, DELAY_TIME_MAX, 5, false, false, true);
#elif DELAY_TIME_MAX >= 100
    display_bar_int("Delay Time", configuration.fx.delay_time[selected_instance_id], 10.0, DELAY_TIME_MIN, DELAY_TIME_MAX, 4, false, false, true);
#else
    display_bar_int("Delay Time", configuration.fx.delay_time[selected_instance_id], 10.0, DELAY_TIME_MIN, DELAY_TIME_MAX, 3, false, false, true);
#endif

    lcd_active_instance_number(selected_instance_id);
    UI_update_instance_icons();
  }

  if (LCDML.FUNC_loop())  // ****** LOOP *********
  {
    if ((LCDML.BT_checkDown() && encoderDir[ENC_R].Down()) || (LCDML.BT_checkUp() && encoderDir[ENC_R].Up()) || (LCDML.BT_checkEnter() && encoderDir[ENC_R].ButtonShort())) {
      if (LCDML.BT_checkDown()) {
        configuration.fx.delay_time[selected_instance_id] = constrain(configuration.fx.delay_time[selected_instance_id] + ENCODER[ENC_R].speed(), DELAY_TIME_MIN, DELAY_TIME_MAX);
        MD_sendControlChange(configuration.dexed[selected_instance_id].midi_channel, 105, configuration.fx.delay_time[selected_instance_id]);
      } else if (LCDML.BT_checkUp()) {
        configuration.fx.delay_time[selected_instance_id] = constrain(configuration.fx.delay_time[selected_instance_id] - ENCODER[ENC_R].speed(), DELAY_TIME_MIN, DELAY_TIME_MAX);
        MD_sendControlChange(configuration.dexed[selected_instance_id].midi_channel, 105, configuration.fx.delay_time[selected_instance_id]);
      }
    }

#if NUM_DEXED > 1
    if (LCDML.BT_checkEnter()) {
      selected_instance_id = !selected_instance_id;
      lcd_active_instance_number(selected_instance_id);
      UI_update_instance_icons();
    }
#endif

#if DELAY_TIME_MAX >= 1000
    display_bar_int("Delay Time", configuration.fx.delay_time[selected_instance_id], 10.0, DELAY_TIME_MIN, DELAY_TIME_MAX, 5, false, false, true);
#elif DELAY_TIME_MAX >= 100
    display_bar_int("Delay Time", configuration.fx.delay_time[selected_instance_id], 10.0, DELAY_TIME_MIN, DELAY_TIME_MAX, 4, false, false, true);
#else
    display_bar_int("Delay Time", configuration.fx.delay_time[selected_instance_id], 10.0, DELAY_TIME_MIN, DELAY_TIME_MAX, 3, false, false, true);
#endif
    delay_fx[selected_instance_id]->delay(0, constrain(configuration.fx.delay_time[selected_instance_id], DELAY_TIME_MIN, DELAY_TIME_MAX) * 10);
  }

  if (LCDML.FUNC_close())  // ****** STABLE END *********
  {
    lcd_special_chars(SCROLLBAR);
    encoderDir[ENC_R].reset();
  }
}

void UI_func_delay_feedback(uint8_t param) {
  if (LCDML.FUNC_setup())  // ****** SETUP *********
  {
    encoderDir[ENC_R].reset();

    lcd_special_chars(BLOCKBAR);
    display_bar_int("Delay Feedb.", configuration.fx.delay_feedback[selected_instance_id], 1.0, DELAY_FEEDBACK_MIN, DELAY_FEEDBACK_MAX, 3, false, false, true);

    lcd_active_instance_number(selected_instance_id);
    UI_update_instance_icons();
  }

  if (LCDML.FUNC_loop())  // ****** LOOP *********
  {
    if ((LCDML.BT_checkDown() && encoderDir[ENC_R].Down()) || (LCDML.BT_checkUp() && encoderDir[ENC_R].Up()) || (LCDML.BT_checkEnter() && encoderDir[ENC_R].ButtonShort())) {
      if (LCDML.BT_checkDown()) {
        configuration.fx.delay_feedback[selected_instance_id] = constrain(configuration.fx.delay_feedback[selected_instance_id] + ENCODER[ENC_R].speed(), DELAY_FEEDBACK_MIN, DELAY_FEEDBACK_MAX);
        MD_sendControlChange(configuration.dexed[selected_instance_id].midi_channel, 106, configuration.fx.delay_feedback[selected_instance_id]);
      } else if (LCDML.BT_checkUp()) {
        configuration.fx.delay_feedback[selected_instance_id] = constrain(configuration.fx.delay_feedback[selected_instance_id] - ENCODER[ENC_R].speed(), DELAY_FEEDBACK_MIN, DELAY_FEEDBACK_MAX);
        MD_sendControlChange(configuration.dexed[selected_instance_id].midi_channel, 106, configuration.fx.delay_feedback[selected_instance_id]);
      }
#if NUM_DEXED > 1
      else if (LCDML.BT_checkEnter()) {
        selected_instance_id = !selected_instance_id;
        lcd_active_instance_number(selected_instance_id);
        UI_update_instance_icons();
      }
#endif
    }

    display_bar_int("Delay Feedb.", configuration.fx.delay_feedback[selected_instance_id], 1.0, DELAY_FEEDBACK_MIN, DELAY_FEEDBACK_MAX, 3, false, false, false);

    delay_fb_mixer[selected_instance_id]->gain(1, midi_volume_transform(map(configuration.fx.delay_feedback[selected_instance_id], DELAY_FEEDBACK_MIN, DELAY_FEEDBACK_MAX, 0, 127)));  // amount of feedback
  }

  if (LCDML.FUNC_close())  // ****** STABLE END *********
  {
    lcd_special_chars(SCROLLBAR);
    encoderDir[ENC_R].reset();
  }
}

void UI_func_delay_level(uint8_t param) {
  if (LCDML.FUNC_setup())  // ****** SETUP *********
  {
    encoderDir[ENC_R].reset();

    lcd_special_chars(BLOCKBAR);
    display_bar_int("Delay Lvl.", configuration.fx.delay_level[selected_instance_id], 1.0, DELAY_LEVEL_MIN, DELAY_LEVEL_MAX, 3, false, false, true);

    lcd_active_instance_number(selected_instance_id);
    UI_update_instance_icons();
  }

  if (LCDML.FUNC_loop())  // ****** LOOP *********
  {
    if ((LCDML.BT_checkDown() && encoderDir[ENC_R].Down()) || (LCDML.BT_checkUp() && encoderDir[ENC_R].Up()) || (LCDML.BT_checkEnter() && encoderDir[ENC_R].ButtonShort())) {
      if (LCDML.BT_checkDown()) {
        configuration.fx.delay_level[selected_instance_id] = constrain(configuration.fx.delay_level[selected_instance_id] + ENCODER[ENC_R].speed(), DELAY_LEVEL_MIN, DELAY_LEVEL_MAX);
        MD_sendControlChange(configuration.dexed[selected_instance_id].midi_channel, 107, configuration.fx.delay_level[selected_instance_id]);
      } else if (LCDML.BT_checkUp()) {
        configuration.fx.delay_level[selected_instance_id] = constrain(configuration.fx.delay_level[selected_instance_id] - ENCODER[ENC_R].speed(), DELAY_LEVEL_MIN, DELAY_LEVEL_MAX);
        MD_sendControlChange(configuration.dexed[selected_instance_id].midi_channel, 107, configuration.fx.delay_level[selected_instance_id]);
      }
#if NUM_DEXED > 1
      else if (LCDML.BT_checkEnter()) {
        selected_instance_id = !selected_instance_id;
        lcd_active_instance_number(selected_instance_id);
        UI_update_instance_icons();
      }
#endif
    }

    display_bar_int("Delay Lvl.", configuration.fx.delay_level[selected_instance_id], 1.0, DELAY_LEVEL_MIN, DELAY_LEVEL_MAX, 3, false, false, false);

    delay_mixer[selected_instance_id]->gain(1, midi_volume_transform(map(configuration.fx.delay_level[selected_instance_id], DELAY_LEVEL_MIN, DELAY_LEVEL_MAX, 0, 127)));
  }

  if (LCDML.FUNC_close())  // ****** STABLE END *********
  {
    lcd_special_chars(SCROLLBAR);
    encoderDir[ENC_R].reset();
  }
}

void UI_func_reverb_send(uint8_t param) {
  if (LCDML.FUNC_setup())  // ****** SETUP *********
  {
    encoderDir[ENC_R].reset();

    lcd_special_chars(BLOCKBAR);
    display_bar_int("Reverb Send", configuration.fx.reverb_send[selected_instance_id], 1.0, REVERB_SEND_MIN, REVERB_SEND_MAX, 3, false, false, true);

    lcd_active_instance_number(selected_instance_id);
    UI_update_instance_icons();
  }

  if (LCDML.FUNC_loop())  // ****** LOOP *********
  {
    if ((LCDML.BT_checkDown() && encoderDir[ENC_R].Down()) || (LCDML.BT_checkUp() && encoderDir[ENC_R].Up()) || (LCDML.BT_checkEnter() && encoderDir[ENC_R].ButtonShort())) {
      if (LCDML.BT_checkDown()) {
        configuration.fx.reverb_send[selected_instance_id] = constrain(configuration.fx.reverb_send[selected_instance_id] + ENCODER[ENC_R].speed(), REVERB_SEND_MIN, REVERB_SEND_MAX);
        MD_sendControlChange(configuration.dexed[selected_instance_id].midi_channel, 91, configuration.fx.reverb_send[selected_instance_id]);
      } else if (LCDML.BT_checkUp()) {
        configuration.fx.reverb_send[selected_instance_id] = constrain(configuration.fx.reverb_send[selected_instance_id] - ENCODER[ENC_R].speed(), REVERB_SEND_MIN, REVERB_SEND_MAX);
        MD_sendControlChange(configuration.dexed[selected_instance_id].midi_channel, 91, configuration.fx.reverb_send[selected_instance_id]);
      }
#if NUM_DEXED > 1
      else if (LCDML.BT_checkEnter()) {
        selected_instance_id = !selected_instance_id;
        lcd_active_instance_number(selected_instance_id);
        UI_update_instance_icons();
      }
#endif
    }

    display_bar_int("Reverb Send", configuration.fx.reverb_send[selected_instance_id], 1.0, REVERB_SEND_MIN, REVERB_SEND_MAX, 3, false, false, false);

    reverb_mixer_r.gain(selected_instance_id, volume_transform(mapfloat(configuration.fx.reverb_send[selected_instance_id], REVERB_SEND_MIN, REVERB_SEND_MAX, 0.0, VOL_MAX_FLOAT)));
    reverb_mixer_l.gain(selected_instance_id, volume_transform(mapfloat(configuration.fx.reverb_send[selected_instance_id], REVERB_SEND_MIN, REVERB_SEND_MAX, 0.0, VOL_MAX_FLOAT)));
  }

  if (LCDML.FUNC_close())  // ****** STABLE END *********
  {
    lcd_special_chars(SCROLLBAR);
    encoderDir[ENC_R].reset();
  }
}

void UI_func_filter_cutoff(uint8_t param) {
  if (LCDML.FUNC_setup())  // ****** SETUP *********
  {
    encoderDir[ENC_R].reset();

    lcd_special_chars(BLOCKBAR);
    display_bar_int("Filter Cutoff", configuration.fx.filter_cutoff[selected_instance_id], 1.0, FILTER_CUTOFF_MIN, FILTER_CUTOFF_MAX, 3, false, false, true);

    lcd_active_instance_number(selected_instance_id);
    UI_update_instance_icons();
  }

  if (LCDML.FUNC_loop())  // ****** LOOP *********
  {
    if ((LCDML.BT_checkDown() && encoderDir[ENC_R].Down()) || (LCDML.BT_checkUp() && encoderDir[ENC_R].Up()) || (LCDML.BT_checkEnter() && encoderDir[ENC_R].ButtonShort())) {
      if (LCDML.BT_checkDown()) {
        configuration.fx.filter_cutoff[selected_instance_id] = constrain(configuration.fx.filter_cutoff[selected_instance_id] + ENCODER[ENC_R].speed(), FILTER_CUTOFF_MIN, FILTER_CUTOFF_MAX);
        MD_sendControlChange(configuration.dexed[selected_instance_id].midi_channel, 104, configuration.fx.filter_cutoff[selected_instance_id]);
      } else if (LCDML.BT_checkUp()) {
        configuration.fx.filter_cutoff[selected_instance_id] = constrain(configuration.fx.filter_cutoff[selected_instance_id] - ENCODER[ENC_R].speed(), FILTER_CUTOFF_MIN, FILTER_CUTOFF_MAX);
        MD_sendControlChange(configuration.dexed[selected_instance_id].midi_channel, 104, configuration.fx.filter_cutoff[selected_instance_id]);
      }
#if NUM_DEXED > 1
      else if (LCDML.BT_checkEnter()) {
        selected_instance_id = !selected_instance_id;
        lcd_active_instance_number(selected_instance_id);
        UI_update_instance_icons();
      }
#endif
    }

    display_bar_int("Filter Cutoff", configuration.fx.filter_cutoff[selected_instance_id], 1.0, FILTER_CUTOFF_MIN, FILTER_CUTOFF_MAX, 3, false, false, false);

    MicroDexed[selected_instance_id]->setFilterCutoff(mapfloat(configuration.fx.filter_cutoff[selected_instance_id], FILTER_CUTOFF_MIN, FILTER_CUTOFF_MAX, 1.0, 0.0));
  }

  if (LCDML.FUNC_close())  // ****** STABLE END *********
  {
    lcd_special_chars(SCROLLBAR);
    encoderDir[ENC_R].reset();
  }
}

void UI_func_filter_resonance(uint8_t param) {
  if (LCDML.FUNC_setup())  // ****** SETUP *********
  {
    encoderDir[ENC_R].reset();

    lcd_special_chars(BLOCKBAR);
    display_bar_int("Filter Reso.", configuration.fx.filter_resonance[selected_instance_id], 1.0, FILTER_RESONANCE_MIN, FILTER_RESONANCE_MAX, 3, false, false, true);

    lcd_active_instance_number(selected_instance_id);
    UI_update_instance_icons();
  }

  if (LCDML.FUNC_loop())  // ****** LOOP *********
  {
    if ((LCDML.BT_checkDown() && encoderDir[ENC_R].Down()) || (LCDML.BT_checkUp() && encoderDir[ENC_R].Up()) || (LCDML.BT_checkEnter() && encoderDir[ENC_R].ButtonShort())) {
      if (LCDML.BT_checkDown()) {
        configuration.fx.filter_resonance[selected_instance_id] = constrain(configuration.fx.filter_resonance[selected_instance_id] + ENCODER[ENC_R].speed(), FILTER_RESONANCE_MIN, FILTER_RESONANCE_MAX);
        MD_sendControlChange(configuration.dexed[selected_instance_id].midi_channel, 103, configuration.fx.filter_resonance[selected_instance_id]);
      } else if (LCDML.BT_checkUp()) {
        configuration.fx.filter_resonance[selected_instance_id] = constrain(configuration.fx.filter_resonance[selected_instance_id] - ENCODER[ENC_R].speed(), FILTER_RESONANCE_MIN, FILTER_RESONANCE_MAX);
        MD_sendControlChange(configuration.dexed[selected_instance_id].midi_channel, 103, configuration.fx.filter_resonance[selected_instance_id]);
      }
#if NUM_DEXED > 1
      else if (LCDML.BT_checkEnter()) {
        selected_instance_id = !selected_instance_id;
        lcd_active_instance_number(selected_instance_id);
        UI_update_instance_icons();
      }
#endif
    }

    display_bar_int("Filter Reso.", configuration.fx.filter_resonance[selected_instance_id], 1.0, FILTER_RESONANCE_MIN, FILTER_RESONANCE_MAX, 3, false, false, false);

    MicroDexed[selected_instance_id]->setFilterResonance(mapfloat(configuration.fx.filter_resonance[selected_instance_id], FILTER_RESONANCE_MIN, FILTER_RESONANCE_MAX, 1.0, 0.0));
  }

  if (LCDML.FUNC_close())  // ****** STABLE END *********
  {
    lcd_special_chars(SCROLLBAR);
    encoderDir[ENC_R].reset();
  }
}

void UI_func_transpose(uint8_t param) {
  if (LCDML.FUNC_setup())  // ****** SETUP *********
  {
    encoderDir[ENC_R].reset();

    lcd_special_chars(METERBAR);
    display_meter_int("Transpose", configuration.dexed[selected_instance_id].transpose, 1.0, -24.0, TRANSPOSE_MIN, TRANSPOSE_MAX, 2, false, true, true);

    lcd_active_instance_number(selected_instance_id);
    UI_update_instance_icons();
  }

  if (LCDML.FUNC_loop())  // ****** LOOP *********
  {
    if ((LCDML.BT_checkDown() && encoderDir[ENC_R].Down()) || (LCDML.BT_checkUp() && encoderDir[ENC_R].Up()) || (LCDML.BT_checkEnter() && encoderDir[ENC_R].ButtonShort())) {
      if (LCDML.BT_checkDown())
        configuration.dexed[selected_instance_id].transpose = constrain(configuration.dexed[selected_instance_id].transpose + ENCODER[ENC_R].speed(), TRANSPOSE_MIN, TRANSPOSE_MAX);
      else if (LCDML.BT_checkUp())
        configuration.dexed[selected_instance_id].transpose = constrain(configuration.dexed[selected_instance_id].transpose - ENCODER[ENC_R].speed(), TRANSPOSE_MIN, TRANSPOSE_MAX);
#if NUM_DEXED > 1
      else if (LCDML.BT_checkEnter()) {
        selected_instance_id = !selected_instance_id;
        lcd_active_instance_number(selected_instance_id);
        UI_update_instance_icons();
      }
#endif
    }

    display_meter_int("Transpose", configuration.dexed[selected_instance_id].transpose, 1.0, -24.0, TRANSPOSE_MIN, TRANSPOSE_MAX, 2, false, true, true);

    MicroDexed[selected_instance_id]->setTranspose(configuration.dexed[selected_instance_id].transpose);
    MicroDexed[selected_instance_id]->notesOff();
    send_sysex_param(configuration.dexed[selected_instance_id].midi_channel, 144, configuration.dexed[selected_instance_id].transpose, 0);
  }

  if (LCDML.FUNC_close())  // ****** STABLE END *********
  {
    lcd_special_chars(SCROLLBAR);
    encoderDir[ENC_R].reset();
  }
}

void UI_func_tune(uint8_t param) {
  if (LCDML.FUNC_setup())  // ****** SETUP *********
  {
    encoderDir[ENC_R].reset();

    lcd_special_chars(METERBAR);
    display_meter_int("Fine Tune", configuration.dexed[selected_instance_id].tune, 1.0, -100.0, TUNE_MIN, TUNE_MAX, 3, false, true, true);

    lcd_active_instance_number(selected_instance_id);
    UI_update_instance_icons();
  }

  if (LCDML.FUNC_loop())  // ****** LOOP *********
  {
    if ((LCDML.BT_checkDown() && encoderDir[ENC_R].Down()) || (LCDML.BT_checkUp() && encoderDir[ENC_R].Up()) || (LCDML.BT_checkEnter() && encoderDir[ENC_R].ButtonShort())) {
      if (LCDML.BT_checkDown()) {
        configuration.dexed[selected_instance_id].tune = constrain(configuration.dexed[selected_instance_id].tune + ENCODER[ENC_R].speed(), TUNE_MIN, TUNE_MAX);
        MD_sendControlChange(configuration.dexed[selected_instance_id].midi_channel, 94, configuration.dexed[selected_instance_id].tune);
      } else if (LCDML.BT_checkUp()) {
        configuration.dexed[selected_instance_id].tune = constrain(configuration.dexed[selected_instance_id].tune - ENCODER[ENC_R].speed(), TUNE_MIN, TUNE_MAX);
        MD_sendControlChange(configuration.dexed[selected_instance_id].midi_channel, 94, configuration.dexed[selected_instance_id].tune);
      }
#if NUM_DEXED > 1
      else if (LCDML.BT_checkEnter()) {
        selected_instance_id = !selected_instance_id;
        lcd_active_instance_number(selected_instance_id);
        UI_update_instance_icons();
      }
#endif
    }

    display_meter_int("Fine Tune", configuration.dexed[selected_instance_id].tune, 1.0, -100.0, TUNE_MIN, TUNE_MAX, 3, false, true, false);

    MicroDexed[selected_instance_id]->setMasterTune((int((configuration.dexed[selected_instance_id].tune - 100) / 100.0 * 0x4000) << 11) * (1.0 / 12));
    MicroDexed[selected_instance_id]->doRefreshVoice();
  }

  if (LCDML.FUNC_close())  // ****** STABLE END *********
  {
    lcd_special_chars(SCROLLBAR);
    encoderDir[ENC_R].reset();
  }
}

void UI_func_midi_channel(uint8_t param) {
  if (LCDML.FUNC_setup())  // ****** SETUP *********
  {
    encoderDir[ENC_R].reset();

    display.setCursor(0, 0);
    display.print(F("MIDI Channel"));

    lcd_active_instance_number(selected_instance_id);
    UI_update_instance_icons();
  }

  if (LCDML.FUNC_loop())  // ****** LOOP *********
  {
    if (LCDML.BT_checkDown() && encoderDir[ENC_R].Down())
      configuration.dexed[selected_instance_id].midi_channel = constrain(configuration.dexed[selected_instance_id].midi_channel + ENCODER[ENC_R].speed(), MIDI_CHANNEL_MIN, MIDI_CHANNEL_MAX);
    else if (LCDML.BT_checkUp() && encoderDir[ENC_R].Up())
      configuration.dexed[selected_instance_id].midi_channel = constrain(configuration.dexed[selected_instance_id].midi_channel - ENCODER[ENC_R].speed(), MIDI_CHANNEL_MIN, MIDI_CHANNEL_MAX);
#if NUM_DEXED > 1
    else if (LCDML.BT_checkEnter() && encoderDir[ENC_R].ButtonShort()) {
      selected_instance_id = !selected_instance_id;
      lcd_active_instance_number(selected_instance_id);
      UI_update_instance_icons();
    }
#endif

    display.setCursor(0, 1);
    if (configuration.dexed[selected_instance_id].midi_channel == 0) {
      display.print(F("[OMNI]"));
    } else {
      display_int(configuration.dexed[selected_instance_id].midi_channel, 4, false, true, false);
    }
  }

  if (LCDML.FUNC_close())  // ****** STABLE END *********
  {
    lcd_special_chars(SCROLLBAR);
    encoderDir[ENC_R].reset();
  }
}

void getNoteName(char* noteName, uint8_t noteNumber) {
  char notes[12][3] = { "A", "A#", "B", "C", "C#", "D", "D#", "E", "F", "F#", "G", "G#" };
  uint8_t oct_index = noteNumber - 12;

  noteNumber -= 21;
  snprintf_P(noteName, sizeof(noteName), PSTR("%2s%1d"), notes[noteNumber % 12], oct_index / 12);
}

void UI_func_lowest_note(uint8_t param) {
  char note_name[4];

  if (LCDML.FUNC_setup())  // ****** SETUP *********
  {
    encoderDir[ENC_R].reset();

    getNoteName(note_name, configuration.dexed[selected_instance_id].lowest_note);
    display.setCursor(0, 0);
    display.print(F("Lowest Note"));
    display.setCursor(0, 1);
    display.print(F("["));
    display.print(note_name);
    display.print(F("]"));

    lcd_active_instance_number(selected_instance_id);
    UI_update_instance_icons();

    midi_learn_mode = MIDI_LEARN_MODE_ON;
  }

  if (LCDML.FUNC_loop())  // ****** LOOP *********
  {
    if ((LCDML.BT_checkDown() && encoderDir[ENC_R].Down()) || (LCDML.BT_checkUp() && encoderDir[ENC_R].Up()) || (LCDML.BT_checkEnter() && encoderDir[ENC_R].ButtonShort())) {
      if (LCDML.BT_checkDown())
        configuration.dexed[selected_instance_id].lowest_note = constrain(configuration.dexed[selected_instance_id].lowest_note + ENCODER[ENC_R].speed(), INSTANCE_LOWEST_NOTE_MIN, INSTANCE_LOWEST_NOTE_MAX);
      else if (LCDML.BT_checkUp())
        configuration.dexed[selected_instance_id].lowest_note = constrain(configuration.dexed[selected_instance_id].lowest_note - ENCODER[ENC_R].speed(), INSTANCE_LOWEST_NOTE_MIN, INSTANCE_LOWEST_NOTE_MAX);
#if NUM_DEXED > 1
      else if (LCDML.BT_checkEnter()) {
        selected_instance_id = !selected_instance_id;
        lcd_active_instance_number(selected_instance_id);
        UI_update_instance_icons();
      }
#endif
    }

    getNoteName(note_name, configuration.dexed[selected_instance_id].lowest_note);
    display.setCursor(1, 1);
    display.print(note_name);
  }

  if (LCDML.FUNC_close())  // ****** STABLE END *********
  {
    lcd_special_chars(SCROLLBAR);
    encoderDir[ENC_R].reset();
    midi_learn_mode = MIDI_LEARN_MODE_OFF;
  }
}

void UI_func_highest_note(uint8_t param) {
  char note_name[4];

  if (LCDML.FUNC_setup())  // ****** SETUP *********
  {
    encoderDir[ENC_R].reset();

    getNoteName(note_name, configuration.dexed[selected_instance_id].highest_note);
    display.setCursor(0, 0);
    display.print(F("Highest Note"));
    display.setCursor(0, 1);
    display.print(F("["));
    display.print(note_name);
    display.print(F("]"));

    lcd_active_instance_number(selected_instance_id);
    UI_update_instance_icons();
    midi_learn_mode = MIDI_LEARN_MODE_ON;
  }

  if (LCDML.FUNC_loop())  // ****** LOOP *********
  {
    if ((LCDML.BT_checkDown() && encoderDir[ENC_R].Down()) || (LCDML.BT_checkUp() && encoderDir[ENC_R].Up()) || (LCDML.BT_checkEnter() && encoderDir[ENC_R].ButtonShort())) {
      if (LCDML.BT_checkDown())
        configuration.dexed[selected_instance_id].highest_note = constrain(configuration.dexed[selected_instance_id].highest_note + ENCODER[ENC_R].speed(), INSTANCE_HIGHEST_NOTE_MIN, INSTANCE_HIGHEST_NOTE_MAX);
      else if (LCDML.BT_checkUp())
        configuration.dexed[selected_instance_id].highest_note = constrain(configuration.dexed[selected_instance_id].highest_note - ENCODER[ENC_R].speed(), INSTANCE_HIGHEST_NOTE_MIN, INSTANCE_HIGHEST_NOTE_MAX);
#if NUM_DEXED > 1
      else if (LCDML.BT_checkEnter()) {
        selected_instance_id = !selected_instance_id;
        lcd_active_instance_number(selected_instance_id);
        UI_update_instance_icons();
      }
#endif
    }

    getNoteName(note_name, configuration.dexed[selected_instance_id].highest_note);
    display.setCursor(1, 1);
    display.print(note_name);
  }

  if (LCDML.FUNC_close())  // ****** STABLE END *********
  {
    lcd_special_chars(SCROLLBAR);
    encoderDir[ENC_R].reset();
    midi_learn_mode = MIDI_LEARN_MODE_OFF;
  }
}

void UI_func_sound_intensity(uint8_t param) {
  if (LCDML.FUNC_setup())  // ****** SETUP *********
  {
    encoderDir[ENC_R].reset();

    lcd_special_chars(BLOCKBAR);
    display_bar_int("Voice Level", configuration.dexed[selected_instance_id].sound_intensity, 1.0, SOUND_INTENSITY_MIN, SOUND_INTENSITY_MAX, 3, false, false, true);

    lcd_active_instance_number(selected_instance_id);
    UI_update_instance_icons();
  }

  if (LCDML.FUNC_loop())  // ****** LOOP *********
  {
    if ((LCDML.BT_checkDown() && encoderDir[ENC_R].Down()) || (LCDML.BT_checkUp() && encoderDir[ENC_R].Up()) || (LCDML.BT_checkEnter() && encoderDir[ENC_R].ButtonShort())) {
      encoderDir[ENC_R].reset();

      if (LCDML.BT_checkDown()) {
        configuration.dexed[selected_instance_id].sound_intensity = constrain(configuration.dexed[selected_instance_id].sound_intensity + ENCODER[ENC_R].speed(), SOUND_INTENSITY_MIN, SOUND_INTENSITY_MAX);
        MD_sendControlChange(configuration.dexed[selected_instance_id].midi_channel, 7, configuration.dexed[selected_instance_id].sound_intensity);
      } else if (LCDML.BT_checkUp()) {
        configuration.dexed[selected_instance_id].sound_intensity = constrain(configuration.dexed[selected_instance_id].sound_intensity - ENCODER[ENC_R].speed(), SOUND_INTENSITY_MIN, SOUND_INTENSITY_MAX);
        MD_sendControlChange(configuration.dexed[selected_instance_id].midi_channel, 7, configuration.dexed[selected_instance_id].sound_intensity);
      }

#if NUM_DEXED > 1
      else if (LCDML.BT_checkEnter()) {
        selected_instance_id = !selected_instance_id;
        lcd_active_instance_number(selected_instance_id);
        UI_update_instance_icons();
      }
#endif
    }

    display_bar_int("Voice Level", configuration.dexed[selected_instance_id].sound_intensity, 1.0, SOUND_INTENSITY_MIN, SOUND_INTENSITY_MAX, 3, false, false, false);
    MicroDexed[selected_instance_id]->setGain(midi_volume_transform(map(configuration.dexed[selected_instance_id].sound_intensity, SOUND_INTENSITY_MIN, SOUND_INTENSITY_MAX, 0, 127)));
  }

  if (LCDML.FUNC_close())  // ****** STABLE END *********
  {
    lcd_special_chars(SCROLLBAR);
    encoderDir[ENC_R].reset();
  }
}

void UI_func_panorama(uint8_t param) {
  if (LCDML.FUNC_setup())  // ****** SETUP *********
  {
    encoderDir[ENC_R].reset();

    if (configuration.sys.mono > 0) {
      display.setCursor(0, 0);
      display.print(F("Panorama"));
      display.setCursor(0, 1);
      display.print(F("MONO-disabled"));
      return;
    }
    lcd_special_chars(METERBAR);
    display_meter_float("Panorama", configuration.dexed[selected_instance_id].pan, 0.05, -20.0, PANORAMA_MIN, PANORAMA_MAX, 1, 1, false, true, true);

    lcd_active_instance_number(selected_instance_id);
    UI_update_instance_icons();
  }

  if (LCDML.FUNC_loop())  // ****** LOOP *********
  {
    if (LCDML.BT_checkDown() && encoderDir[ENC_R].Down() && configuration.sys.mono == 0) {
      configuration.dexed[selected_instance_id].pan = constrain(configuration.dexed[selected_instance_id].pan + ENCODER[ENC_R].speed(), PANORAMA_MIN, PANORAMA_MAX);
      MD_sendControlChange(configuration.dexed[selected_instance_id].midi_channel, 10, map(configuration.dexed[selected_instance_id].pan, PANORAMA_MIN, PANORAMA_MAX, 0, 127));
    } else if (LCDML.BT_checkUp() && encoderDir[ENC_R].Up() && configuration.sys.mono == 0) {
      configuration.dexed[selected_instance_id].pan = constrain(configuration.dexed[selected_instance_id].pan - ENCODER[ENC_R].speed(), PANORAMA_MIN, PANORAMA_MAX);
      MD_sendControlChange(configuration.dexed[selected_instance_id].midi_channel, 10, map(configuration.dexed[selected_instance_id].pan, PANORAMA_MIN, PANORAMA_MAX, 0, 127));
    }
#if NUM_DEXED > 1
    else if (LCDML.BT_checkEnter() && encoderDir[ENC_R].ButtonShort()) {
      selected_instance_id = !selected_instance_id;
      lcd_active_instance_number(selected_instance_id);
      UI_update_instance_icons();
    }
#endif

    if (configuration.sys.mono == 0) {
      display_meter_float("Panorama", configuration.dexed[selected_instance_id].pan, 0.05, -20.0, PANORAMA_MIN, PANORAMA_MAX, 1, 1, false, true, false);
      mono2stereo[selected_instance_id]->panorama(mapfloat(configuration.dexed[selected_instance_id].pan, PANORAMA_MIN, PANORAMA_MAX, -1.0, 1.0));
    }
  }

  if (LCDML.FUNC_close())  // ****** STABLE END *********
  {
    lcd_special_chars(SCROLLBAR);
    encoderDir[ENC_R].reset();
  }
}

void UI_func_favorites(uint8_t param) {
  static uint8_t old_favorites;

  if (LCDML.FUNC_setup())  // ****** SETUP *********
  {
    encoderDir[ENC_L].reset();
    old_favorites = configuration.sys.favorites;

    display.setCursor(0, 0);
    display.print(F("Favorites"));
    display.setCursor(0, 1);
    switch (configuration.sys.favorites) {
      case 0:
        display.print(F("[ All  presets ]"));
        break;
      case 1:
        display.print(F("[  FAVs. only  ]"));
        break;
      case 2:
        display.print(F("[non-FAVs. only]"));
        break;
      case 3:
        display.print(F("[random non-FAV]"));
        break;
    }
  }

  if (LCDML.FUNC_loop())  // ****** LOOP *********
  {
    if (LCDML.BT_checkDown())
      configuration.sys.favorites = constrain(configuration.sys.favorites + 1, 0, 3);
    else if (LCDML.BT_checkUp())
      configuration.sys.favorites = constrain(configuration.sys.favorites - 1, 0, 3);

    display.setCursor(0, 1);
    switch (configuration.sys.favorites) {
      case 0:
        display.print(F("[ All  presets ]"));
        break;
      case 1:
        display.print(F("[  FAVs. only  ]"));
        break;
      case 2:
        display.print(F("[non-FAVs. only]"));
        break;
      case 3:
        display.print(F("[random non-FAV]"));
        break;
    }
  }

  if (LCDML.FUNC_close())  // ****** STABLE END *********
  {
    lcd_special_chars(SCROLLBAR);
    encoderDir[ENC_L].reset();
    if (old_favorites != configuration.sys.favorites) {
      save_sys_flag = true;
      save_sys = 0;
    }
  }
}

void UI_func_epiano_midi_channel(uint8_t param) {
  if (LCDML.FUNC_setup())  // ****** SETUP *********
  {
    encoderDir[ENC_R].reset();

    display.setCursor(0, 0);
    display.print(F("EP MIDI Channel"));
  }

  if (LCDML.FUNC_loop())  // ****** LOOP *********
  {
    if (LCDML.BT_checkDown() && encoderDir[ENC_R].Down())
      configuration.epiano.midi_channel = constrain(configuration.epiano.midi_channel + ENCODER[ENC_R].speed(), EP_MIDI_CHANNEL_MIN, EP_MIDI_CHANNEL_MAX);
    else if (LCDML.BT_checkUp() && encoderDir[ENC_R].Up())
      configuration.epiano.midi_channel = constrain(configuration.epiano.midi_channel - ENCODER[ENC_R].speed(), EP_MIDI_CHANNEL_MIN, EP_MIDI_CHANNEL_MAX);

    display.setCursor(0, 1);
    if (configuration.epiano.midi_channel == 0) {
      display.print(F("[OMNI]"));
    } else {
      display_int(configuration.epiano.midi_channel, 4, false, true, false);
    }
  }

  if (LCDML.FUNC_close())  // ****** STABLE END *********
  {
    lcd_special_chars(SCROLLBAR);
    encoderDir[ENC_R].reset();
  }
}

void UI_func_epiano_lowest_note(uint8_t param) {
  char note_name[4];

  if (LCDML.FUNC_setup())  // ****** SETUP *********
  {
    encoderDir[ENC_R].reset();
    midi_learn_mode = MIDI_LEARN_MODE_ON;

    getNoteName(note_name, configuration.epiano.lowest_note);
    display.setCursor(0, 0);
    display.print(F("EP Lowest Note"));
    display.setCursor(0, 1);
    display.print(F("["));
    display.print(note_name);
    display.print(F("]"));
  }

  if (LCDML.FUNC_loop())  // ****** LOOP *********
  {
    if ((LCDML.BT_checkDown() && encoderDir[ENC_R].Down()) || (LCDML.BT_checkUp() && encoderDir[ENC_R].Up()) || (LCDML.BT_checkEnter() && encoderDir[ENC_R].ButtonShort())) {
      if (LCDML.BT_checkDown())
        configuration.epiano.lowest_note = constrain(configuration.epiano.lowest_note + ENCODER[ENC_R].speed(), EP_LOWEST_NOTE_MIN, EP_LOWEST_NOTE_MAX);
      else if (LCDML.BT_checkUp())
        configuration.epiano.lowest_note = constrain(configuration.epiano.lowest_note - ENCODER[ENC_R].speed(), EP_LOWEST_NOTE_MIN, EP_LOWEST_NOTE_MAX);
    }

    getNoteName(note_name, configuration.epiano.lowest_note);
    display.setCursor(1, 1);
    display.print(note_name);
  }

  if (LCDML.FUNC_close())  // ****** STABLE END *********
  {
    lcd_special_chars(SCROLLBAR);
    encoderDir[ENC_R].reset();
    midi_learn_mode = MIDI_LEARN_MODE_OFF;
  }
}

void UI_func_epiano_highest_note(uint8_t param) {
  char note_name[4];

  if (LCDML.FUNC_setup())  // ****** SETUP *********
  {
    encoderDir[ENC_R].reset();
    midi_learn_mode = MIDI_LEARN_MODE_ON;

    getNoteName(note_name, configuration.dexed[selected_instance_id].highest_note);
    display.setCursor(0, 0);
    display.print(F("EP Highest Note"));
    display.setCursor(0, 1);
    display.print(F("["));
    display.print(note_name);
    display.print(F("]"));
  }

  if (LCDML.FUNC_loop())  // ****** LOOP *********
  {
    if ((LCDML.BT_checkDown() && encoderDir[ENC_R].Down()) || (LCDML.BT_checkUp() && encoderDir[ENC_R].Up()) || (LCDML.BT_checkEnter() && encoderDir[ENC_R].ButtonShort())) {
      if (LCDML.BT_checkDown())
        configuration.epiano.highest_note = constrain(configuration.epiano.highest_note + ENCODER[ENC_R].speed(), EP_HIGHEST_NOTE_MIN, EP_HIGHEST_NOTE_MAX);
      else if (LCDML.BT_checkUp())
        configuration.epiano.highest_note = constrain(configuration.epiano.highest_note - ENCODER[ENC_R].speed(), EP_HIGHEST_NOTE_MIN, EP_HIGHEST_NOTE_MAX);
    }

    getNoteName(note_name, configuration.epiano.highest_note);
    display.setCursor(1, 1);
    display.print(note_name);
  }

  if (LCDML.FUNC_close())  // ****** STABLE END *********
  {
    lcd_special_chars(SCROLLBAR);
    encoderDir[ENC_R].reset();
    midi_learn_mode = MIDI_LEARN_MODE_OFF;
  }
}

void UI_func_epiano_sound_intensity(uint8_t param) {
  if (LCDML.FUNC_setup())  // ****** SETUP *********
  {
    encoderDir[ENC_R].reset();

    lcd_special_chars(BLOCKBAR);
    display_bar_int("EP Level", configuration.epiano.sound_intensity, 1.0, EP_SOUND_INTENSITY_MIN, EP_SOUND_INTENSITY_MAX, 3, false, false, true);
  }

  if (LCDML.FUNC_loop())  // ****** LOOP *********
  {
    if ((LCDML.BT_checkDown() && encoderDir[ENC_R].Down()) || (LCDML.BT_checkUp() && encoderDir[ENC_R].Up()) || (LCDML.BT_checkEnter() && encoderDir[ENC_R].ButtonShort())) {
      encoderDir[ENC_R].reset();

      if (LCDML.BT_checkDown()) {
        configuration.epiano.sound_intensity = constrain(configuration.epiano.sound_intensity + ENCODER[ENC_R].speed(), EP_SOUND_INTENSITY_MIN, EP_SOUND_INTENSITY_MAX);
        MD_sendControlChange(configuration.epiano.midi_channel, 7, configuration.epiano.sound_intensity);
      } else if (LCDML.BT_checkUp()) {
        configuration.epiano.sound_intensity = constrain(configuration.epiano.sound_intensity - ENCODER[ENC_R].speed(), EP_SOUND_INTENSITY_MIN, EP_SOUND_INTENSITY_MAX);
        MD_sendControlChange(configuration.epiano.midi_channel, 7, configuration.epiano.sound_intensity);
      }
    }

    display_bar_int("EP Level", configuration.epiano.sound_intensity, 1.0, EP_SOUND_INTENSITY_MIN, EP_SOUND_INTENSITY_MAX, 3, false, false, false);
    ep.setVolume(mapfloat(configuration.epiano.sound_intensity, EP_SOUND_INTENSITY_MIN, EP_SOUND_INTENSITY_MAX, 0, 1.0));
  }

  if (LCDML.FUNC_close())  // ****** STABLE END *********
  {
    lcd_special_chars(SCROLLBAR);
    encoderDir[ENC_R].reset();
  }
}

void UI_func_epiano_panorama(uint8_t param) {
  if (LCDML.FUNC_setup())  // ****** SETUP *********
  {
    encoderDir[ENC_R].reset();

    if (configuration.sys.mono > 0) {
      display.setCursor(0, 0);
      display.print(F("EP Panorama"));
      display.setCursor(0, 1);
      display.print(F("MONO-disabled"));
      return;
    }

    lcd_special_chars(METERBAR);
    display_meter_float("EP Panorama", configuration.epiano.pan, 0.05, -20.0, EP_PANORAMA_MIN, EP_PANORAMA_MAX, 1, 1, false, true, true);
  }

  if (LCDML.FUNC_loop())  // ****** LOOP *********
  {
    if (LCDML.BT_checkDown() && encoderDir[ENC_R].Down() && configuration.sys.mono == 0) {
      configuration.epiano.pan = constrain(configuration.epiano.pan + ENCODER[ENC_R].speed(), EP_PANORAMA_MIN, EP_PANORAMA_MAX);
      MD_sendControlChange(configuration.epiano.midi_channel, 10, map(configuration.epiano.pan, EP_PANORAMA_MIN, EP_PANORAMA_MAX, 0, 127));
    } else if (LCDML.BT_checkUp() && encoderDir[ENC_R].Up() && configuration.sys.mono == 0) {
      configuration.epiano.pan = constrain(configuration.epiano.pan - ENCODER[ENC_R].speed(), EP_PANORAMA_MIN, EP_PANORAMA_MAX);
      MD_sendControlChange(configuration.epiano.midi_channel, 10, map(configuration.epiano.pan, EP_PANORAMA_MIN, EP_PANORAMA_MAX, 0, 127));
    }

    if (configuration.sys.mono == 0) {
      display_meter_float("EP Panorama", configuration.epiano.pan, 0.05, -20.0, EP_PANORAMA_MIN, EP_PANORAMA_MAX, 1, 1, false, true, false);
      ep_stereo_panorama.panorama(mapfloat(configuration.epiano.pan, PANORAMA_MIN, PANORAMA_MAX, -1.0, 1.0));
    }
  }

  if (LCDML.FUNC_close())  // ****** STABLE END *********
  {
    lcd_special_chars(SCROLLBAR);
    encoderDir[ENC_R].reset();
  }
}

void UI_func_epiano_decay(uint8_t param) {
  if (LCDML.FUNC_setup())  // ****** SETUP *********
  {
    encoderDir[ENC_R].reset();

    lcd_special_chars(BLOCKBAR);
    display_bar_int("EP Decay", configuration.epiano.decay, 1.0, EP_DECAY_MIN, EP_DECAY_MAX, 3, false, false, true);
  }

  if (LCDML.FUNC_loop())  // ****** LOOP *********
  {
    if ((LCDML.BT_checkDown() && encoderDir[ENC_R].Down()) || (LCDML.BT_checkUp() && encoderDir[ENC_R].Up()) || (LCDML.BT_checkEnter() && encoderDir[ENC_R].ButtonShort())) {
      encoderDir[ENC_R].reset();

      if (LCDML.BT_checkDown()) {
        configuration.epiano.decay = constrain(configuration.epiano.decay + ENCODER[ENC_R].speed(), EP_DECAY_MIN, EP_DECAY_MAX);
      } else if (LCDML.BT_checkUp()) {
        configuration.epiano.decay = constrain(configuration.epiano.decay - ENCODER[ENC_R].speed(), EP_DECAY_MIN, EP_DECAY_MAX);
      }
    }

    display_bar_int("EP Decay", configuration.epiano.decay, 1.0, EP_DECAY_MIN, EP_DECAY_MAX, 3, false, false, false);
    ep.setDecay(mapfloat(configuration.epiano.decay, EP_DECAY_MIN, EP_DECAY_MAX, 0, 1.0));
  }

  if (LCDML.FUNC_close())  // ****** STABLE END *********
  {
    lcd_special_chars(SCROLLBAR);
    encoderDir[ENC_R].reset();
  }
}

void UI_func_epiano_release(uint8_t param) {
  if (LCDML.FUNC_setup())  // ****** SETUP *********
  {
    encoderDir[ENC_R].reset();

    lcd_special_chars(BLOCKBAR);
    display_bar_int("EP Release", configuration.epiano.release, 1.0, EP_RELEASE_MIN, EP_RELEASE_MAX, 3, false, false, true);
  }

  if (LCDML.FUNC_loop())  // ****** LOOP *********
  {
    if ((LCDML.BT_checkDown() && encoderDir[ENC_R].Down()) || (LCDML.BT_checkUp() && encoderDir[ENC_R].Up())) {
      encoderDir[ENC_R].reset();

      if (LCDML.BT_checkDown()) {
        configuration.epiano.release = constrain(configuration.epiano.release + ENCODER[ENC_R].speed(), EP_RELEASE_MIN, EP_RELEASE_MAX);
      } else if (LCDML.BT_checkUp()) {
        configuration.epiano.release = constrain(configuration.epiano.release - ENCODER[ENC_R].speed(), EP_RELEASE_MIN, EP_RELEASE_MAX);
      }
    }

    display_bar_int("EP Release", configuration.epiano.release, 1.0, EP_RELEASE_MIN, EP_RELEASE_MAX, 3, false, false, false);
    ep.setRelease(mapfloat(configuration.epiano.release, EP_RELEASE_MIN, EP_RELEASE_MAX, 0, 1.0));
  }

  if (LCDML.FUNC_close())  // ****** STABLE END *********
  {
    lcd_special_chars(SCROLLBAR);
    encoderDir[ENC_R].reset();
  }
}

void UI_func_epiano_hardness(uint8_t param) {
  if (LCDML.FUNC_setup())  // ****** SETUP *********
  {
    encoderDir[ENC_R].reset();

    lcd_special_chars(BLOCKBAR);
    display_bar_int("EP Hardness", configuration.epiano.hardness, 1.0, EP_HARDNESS_MIN, EP_HARDNESS_MAX, 3, false, false, true);
  }

  if (LCDML.FUNC_loop())  // ****** LOOP *********
  {
    if ((LCDML.BT_checkDown() && encoderDir[ENC_R].Down()) || (LCDML.BT_checkUp() && encoderDir[ENC_R].Up()) || (LCDML.BT_checkEnter() && encoderDir[ENC_R].ButtonShort())) {
      encoderDir[ENC_R].reset();

      if (LCDML.BT_checkDown()) {
        configuration.epiano.hardness = constrain(configuration.epiano.hardness + ENCODER[ENC_R].speed(), EP_HARDNESS_MIN, EP_HARDNESS_MAX);
      } else if (LCDML.BT_checkUp()) {
        configuration.epiano.hardness = constrain(configuration.epiano.hardness - ENCODER[ENC_R].speed(), EP_HARDNESS_MIN, EP_HARDNESS_MAX);
      }
    }

    display_bar_int("EP Hardness", configuration.epiano.hardness, 1.0, EP_HARDNESS_MIN, EP_HARDNESS_MAX, 3, false, false, false);
    ep.setHardness(mapfloat(configuration.epiano.hardness, EP_HARDNESS_MIN, EP_HARDNESS_MAX, 0, 1.0));
  }

  if (LCDML.FUNC_close())  // ****** STABLE END *********
  {
    lcd_special_chars(SCROLLBAR);
    encoderDir[ENC_R].reset();
  }
}

void UI_func_epiano_treble(uint8_t param) {
  if (LCDML.FUNC_setup())  // ****** SETUP *********
  {
    encoderDir[ENC_R].reset();

    lcd_special_chars(BLOCKBAR);
    display_bar_int("EP Treble", configuration.epiano.treble, 1.0, EP_TREBLE_MIN, EP_TREBLE_MAX, 3, false, false, true);
  }

  if (LCDML.FUNC_loop())  // ****** LOOP *********
  {
    if ((LCDML.BT_checkDown() && encoderDir[ENC_R].Down()) || (LCDML.BT_checkUp() && encoderDir[ENC_R].Up()) || (LCDML.BT_checkEnter() && encoderDir[ENC_R].ButtonShort())) {
      encoderDir[ENC_R].reset();

      if (LCDML.BT_checkDown()) {
        configuration.epiano.treble = constrain(configuration.epiano.treble + ENCODER[ENC_R].speed(), EP_TREBLE_MIN, EP_TREBLE_MAX);
      } else if (LCDML.BT_checkUp()) {
        configuration.epiano.treble = constrain(configuration.epiano.treble - ENCODER[ENC_R].speed(), EP_TREBLE_MIN, EP_TREBLE_MAX);
      }
    }

    display_bar_int("EP Treble", configuration.epiano.treble, 1.0, EP_TREBLE_MIN, EP_TREBLE_MAX, 3, false, false, false);
    ep.setTreble(mapfloat(configuration.epiano.treble, EP_TREBLE_MIN, EP_TREBLE_MAX, 0, 1.0));
  }

  if (LCDML.FUNC_close())  // ****** STABLE END *********
  {
    lcd_special_chars(SCROLLBAR);
    encoderDir[ENC_R].reset();
  }
}

void UI_func_epiano_stereo(uint8_t param) {
  if (LCDML.FUNC_setup())  // ****** SETUP *********
  {
    encoderDir[ENC_R].reset();

    lcd_special_chars(BLOCKBAR);
    display_bar_int("EP Stereo", configuration.epiano.stereo, 1.0, EP_STEREO_MIN, EP_STEREO_MAX, 3, false, false, true);
  }

  if (LCDML.FUNC_loop())  // ****** LOOP *********
  {
    if ((LCDML.BT_checkDown() && encoderDir[ENC_R].Down()) || (LCDML.BT_checkUp() && encoderDir[ENC_R].Up()) || (LCDML.BT_checkEnter() && encoderDir[ENC_R].ButtonShort())) {
      encoderDir[ENC_R].reset();

      if (LCDML.BT_checkDown()) {
        configuration.epiano.stereo = constrain(configuration.epiano.stereo + ENCODER[ENC_R].speed(), EP_STEREO_MIN, EP_STEREO_MAX);
      } else if (LCDML.BT_checkUp()) {
        configuration.epiano.stereo = constrain(configuration.epiano.stereo - ENCODER[ENC_R].speed(), EP_STEREO_MIN, EP_STEREO_MAX);
      }
    }

    display_bar_int("EP Stereo", configuration.epiano.stereo, 1.0, EP_STEREO_MIN, EP_STEREO_MAX, 3, false, false, false);
    ep.setStereo(mapfloat(configuration.epiano.stereo, EP_STEREO_MIN, EP_STEREO_MAX, 0, 1.0));
  }

  if (LCDML.FUNC_close())  // ****** STABLE END *********
  {
    lcd_special_chars(SCROLLBAR);
    encoderDir[ENC_R].reset();
  }
}

void UI_func_epiano_tune(uint8_t param) {
  if (LCDML.FUNC_setup())  // ****** SETUP *********
  {
    encoderDir[ENC_R].reset();

    lcd_special_chars(METERBAR);
    display_bar_int("EP Tune", configuration.epiano.tune, 1.0, EP_TUNE_MIN, EP_TUNE_MAX, 3, false, true, true);
  }

  if (LCDML.FUNC_loop())  // ****** LOOP *********
  {
    if ((LCDML.BT_checkDown() && encoderDir[ENC_R].Down()) || (LCDML.BT_checkUp() && encoderDir[ENC_R].Up()) || (LCDML.BT_checkEnter() && encoderDir[ENC_R].ButtonShort())) {
      if (LCDML.BT_checkDown()) {
        configuration.epiano.tune = constrain(configuration.epiano.tune + ENCODER[ENC_R].speed(), EP_TUNE_MIN, EP_TUNE_MAX);
        MD_sendControlChange(configuration.epiano.midi_channel, 94, configuration.epiano.tune);
      } else if (LCDML.BT_checkUp()) {
        configuration.epiano.tune = constrain(configuration.epiano.tune - ENCODER[ENC_R].speed(), EP_TUNE_MIN, EP_TUNE_MAX);
        MD_sendControlChange(configuration.epiano.midi_channel, 94, configuration.epiano.tune);
      }
    }

    display_bar_int("EP Tune", configuration.epiano.tune, 1.0, EP_TUNE_MIN, EP_TUNE_MAX, 3, false, true, false);
    ep.setTune(mapfloat(configuration.epiano.tune, EP_TUNE_MIN, EP_TUNE_MAX, 0.0, 1.0));
  }

  if (LCDML.FUNC_close())  // ****** STABLE END *********
  {
    lcd_special_chars(SCROLLBAR);
    encoderDir[ENC_R].reset();
  }
}

void UI_func_epiano_detune(uint8_t param) {
  if (LCDML.FUNC_setup())  // ****** SETUP *********
  {
    encoderDir[ENC_R].reset();

    lcd_special_chars(BLOCKBAR);
    display_bar_int("EP Detune", configuration.epiano.detune, 1.0, EP_DETUNE_MIN, EP_DETUNE_MAX, 3, false, false, true);
  }

  if (LCDML.FUNC_loop())  // ****** LOOP *********
  {
    if ((LCDML.BT_checkDown() && encoderDir[ENC_R].Down()) || (LCDML.BT_checkUp() && encoderDir[ENC_R].Up()) || (LCDML.BT_checkEnter() && encoderDir[ENC_R].ButtonShort())) {
      encoderDir[ENC_R].reset();

      if (LCDML.BT_checkDown()) {
        configuration.epiano.detune = constrain(configuration.epiano.detune + ENCODER[ENC_R].speed(), EP_DETUNE_MIN, EP_DETUNE_MAX);
      } else if (LCDML.BT_checkUp()) {
        configuration.epiano.detune = constrain(configuration.epiano.detune - ENCODER[ENC_R].speed(), EP_DETUNE_MIN, EP_DETUNE_MAX);
      }
    }

    display_bar_int("EP Detune", configuration.epiano.detune, 1.0, EP_DETUNE_MIN, EP_DETUNE_MAX, 3, false, false, false);
    ep.setDetune(mapfloat(configuration.epiano.detune, EP_DETUNE_MIN, EP_DETUNE_MAX, 0, 1.0));
  }

  if (LCDML.FUNC_close())  // ****** STABLE END *********
  {
    lcd_special_chars(SCROLLBAR);
    encoderDir[ENC_R].reset();
  }
}

void UI_func_epiano_pan_tremolo(uint8_t param) {
  if (LCDML.FUNC_setup())  // ****** SETUP *********
  {
    encoderDir[ENC_R].reset();

    lcd_special_chars(BLOCKBAR);
    display_bar_int("EP Trem. Width", configuration.epiano.pan_tremolo, 1.0, EP_PAN_TREMOLO_MIN, EP_PAN_TREMOLO_MAX, 3, false, false, true);
  }

  if (LCDML.FUNC_loop())  // ****** LOOP *********
  {
    if ((LCDML.BT_checkDown() && encoderDir[ENC_R].Down()) || (LCDML.BT_checkUp() && encoderDir[ENC_R].Up())) {
      encoderDir[ENC_R].reset();

      if (LCDML.BT_checkDown()) {
        configuration.epiano.pan_tremolo = constrain(configuration.epiano.pan_tremolo + ENCODER[ENC_R].speed(), EP_PAN_TREMOLO_MIN, EP_PAN_TREMOLO_MAX);
      } else if (LCDML.BT_checkUp()) {
        configuration.epiano.pan_tremolo = constrain(configuration.epiano.pan_tremolo - ENCODER[ENC_R].speed(), EP_PAN_TREMOLO_MIN, EP_PAN_TREMOLO_MAX);
      }
    }

    display_bar_int("EP Trem. Width", configuration.epiano.pan_tremolo, 1.0, EP_PAN_TREMOLO_MIN, EP_PAN_TREMOLO_MAX, 3, false, false, false);
    if (configuration.epiano.pan_tremolo == 0)
      ep.setPanTremolo(0.0);
    else
      ep.setPanTremolo(mapfloat(configuration.epiano.pan_tremolo, EP_PAN_TREMOLO_MIN, EP_PAN_TREMOLO_MAX, 0.0, 1.0));
  }

  if (LCDML.FUNC_close())  // ****** STABLE END *********
  {
    lcd_special_chars(SCROLLBAR);
    encoderDir[ENC_R].reset();
  }
}

void UI_func_epiano_pan_lfo(uint8_t param) {
  if (LCDML.FUNC_setup())  // ****** SETUP *********
  {
    encoderDir[ENC_R].reset();

    lcd_special_chars(BLOCKBAR);
    display_bar_int("EP LFO", configuration.epiano.pan_lfo, 1.0, EP_PAN_LFO_MIN, EP_PAN_LFO_MAX, 3, false, false, true);
  }

  if (LCDML.FUNC_loop())  // ****** LOOP *********
  {
    if ((LCDML.BT_checkDown() && encoderDir[ENC_R].Down()) || (LCDML.BT_checkUp() && encoderDir[ENC_R].Up())) {
      encoderDir[ENC_R].reset();

      if (LCDML.BT_checkDown()) {
        configuration.epiano.pan_lfo = constrain(configuration.epiano.pan_lfo + ENCODER[ENC_R].speed(), EP_PAN_LFO_MIN, EP_PAN_LFO_MAX);
      } else if (LCDML.BT_checkUp()) {
        configuration.epiano.pan_lfo = constrain(configuration.epiano.pan_lfo - ENCODER[ENC_R].speed(), EP_PAN_LFO_MIN, EP_PAN_LFO_MAX);
      }
    }

    display_bar_int("EP LFO", configuration.epiano.pan_lfo, 1.0, EP_PAN_LFO_MIN, EP_PAN_LFO_MAX, 3, false, false, false);
    if (configuration.epiano.pan_lfo == 0)
      ep.setPanLFO(0.0);
    else
      ep.setPanLFO(mapfloat(configuration.epiano.pan_lfo, EP_PAN_LFO_MIN, EP_PAN_LFO_MAX, 0.0, 1.0));
  }

  if (LCDML.FUNC_close())  // ****** STABLE END *********
  {
    lcd_special_chars(SCROLLBAR);
    encoderDir[ENC_R].reset();
  }
}

void UI_func_epiano_overdrive(uint8_t param) {
  if (LCDML.FUNC_setup())  // ****** SETUP *********
  {
    encoderDir[ENC_R].reset();

    lcd_special_chars(BLOCKBAR);
    display_bar_int("EP Overdrive", configuration.epiano.overdrive, 1.0, EP_OVERDRIVE_MIN, EP_OVERDRIVE_MAX, 3, false, false, true);
  }

  if (LCDML.FUNC_loop())  // ****** LOOP *********
  {
    if ((LCDML.BT_checkDown() && encoderDir[ENC_R].Down()) || (LCDML.BT_checkUp() && encoderDir[ENC_R].Up())) {
      encoderDir[ENC_R].reset();

      if (LCDML.BT_checkDown()) {
        configuration.epiano.overdrive = constrain(configuration.epiano.overdrive + ENCODER[ENC_R].speed(), EP_OVERDRIVE_MIN, EP_OVERDRIVE_MAX);
      } else if (LCDML.BT_checkUp()) {
        configuration.epiano.overdrive = constrain(configuration.epiano.overdrive - ENCODER[ENC_R].speed(), EP_OVERDRIVE_MIN, EP_OVERDRIVE_MAX);
      }
    }

    display_bar_int("EP Overdrive", configuration.epiano.overdrive, 1.0, EP_OVERDRIVE_MIN, EP_OVERDRIVE_MAX, 3, false, false, false);
    ep.setOverdrive(mapfloat(configuration.epiano.overdrive, EP_OVERDRIVE_MIN, EP_OVERDRIVE_MAX, 0, 1.0));
  }

  if (LCDML.FUNC_close())  // ****** STABLE END *********
  {
    lcd_special_chars(SCROLLBAR);
    encoderDir[ENC_R].reset();
  }
}

void UI_func_epiano_transpose(uint8_t param) {
  if (LCDML.FUNC_setup())  // ****** SETUP *********
  {
    encoderDir[ENC_R].reset();

    lcd_special_chars(METERBAR);
    display_meter_int("EP Transpose", configuration.epiano.transpose, 1.0, -24.0, EP_TRANSPOSE_MIN, EP_TRANSPOSE_MAX, 2, false, true, true);
  }

  if (LCDML.FUNC_loop())  // ****** LOOP *********
  {
    if ((LCDML.BT_checkDown() && encoderDir[ENC_R].Down()) || (LCDML.BT_checkUp() && encoderDir[ENC_R].Up()) || (LCDML.BT_checkEnter() && encoderDir[ENC_R].ButtonShort())) {
      if (LCDML.BT_checkDown())
        configuration.epiano.transpose = constrain(configuration.epiano.transpose + ENCODER[ENC_R].speed(), EP_TRANSPOSE_MIN, EP_TRANSPOSE_MAX);
      else if (LCDML.BT_checkUp())
        configuration.epiano.transpose = constrain(configuration.epiano.transpose - ENCODER[ENC_R].speed(), EP_TRANSPOSE_MIN, EP_TRANSPOSE_MAX);
    }

    display_meter_int("EP Transpose", configuration.epiano.transpose, 1.0, -24.0, EP_TRANSPOSE_MIN, EP_TRANSPOSE_MAX, 2, false, true, true);
  }

  if (LCDML.FUNC_close())  // ****** STABLE END *********
  {
    lcd_special_chars(SCROLLBAR);
    encoderDir[ENC_R].reset();
  }
}

void UI_func_epiano_polyphony(uint8_t param) {
  if (LCDML.FUNC_setup())  // ****** SETUP *********
  {
    encoderDir[ENC_R].reset();

    lcd_special_chars(BLOCKBAR);
    display_bar_int("EP Polyphony", configuration.epiano.polyphony, 1.0, EP_POLYPHONY_MIN, EP_POLYPHONY_MAX, 2, false, false, true);
  }

  if (LCDML.FUNC_loop())  // ****** LOOP *********
  {
    if ((LCDML.BT_checkDown() && encoderDir[ENC_R].Down()) || (LCDML.BT_checkUp() && encoderDir[ENC_R].Up())) {
      if (LCDML.BT_checkDown()) {
        configuration.epiano.polyphony = constrain(configuration.epiano.polyphony + 1, EP_POLYPHONY_MIN, EP_POLYPHONY_MAX);
      } else if (LCDML.BT_checkUp()) {
        if (configuration.epiano.polyphony - 1 < 1)
          configuration.epiano.polyphony = 1;
        else {
          configuration.epiano.polyphony = constrain(configuration.epiano.polyphony - 1, EP_POLYPHONY_MIN, EP_POLYPHONY_MAX);
        }
      }
    }

    display_bar_int("EP Polyphony", configuration.epiano.polyphony, 1.0, EP_POLYPHONY_MIN, EP_POLYPHONY_MAX, 2, false, false, false);
    ep.setPolyphony(configuration.epiano.polyphony);
  }

  if (LCDML.FUNC_close())  // ****** STABLE END *********
  {
    lcd_special_chars(SCROLLBAR);
    encoderDir[ENC_R].reset();
  }
}

void UI_func_epiano_velocity_sense(uint8_t param) {
  if (LCDML.FUNC_setup())  // ****** SETUP *********
  {
    encoderDir[ENC_R].reset();

    lcd_special_chars(BLOCKBAR);
    display_bar_int("EP Vel. Sense", configuration.epiano.velocity_sense, 1.0, EP_VELOCITY_SENSE_MIN, EP_VELOCITY_SENSE_MAX, 3, false, false, true);
  }

  if (LCDML.FUNC_loop())  // ****** LOOP *********
  {
    if ((LCDML.BT_checkDown() && encoderDir[ENC_R].Down()) || (LCDML.BT_checkUp() && encoderDir[ENC_R].Up()) || (LCDML.BT_checkEnter() && encoderDir[ENC_R].ButtonShort())) {
      encoderDir[ENC_R].reset();

      if (LCDML.BT_checkDown()) {
        configuration.epiano.velocity_sense = constrain(configuration.epiano.velocity_sense + ENCODER[ENC_R].speed(), EP_VELOCITY_SENSE_MIN, EP_VELOCITY_SENSE_MAX);
      } else if (LCDML.BT_checkUp()) {
        configuration.epiano.velocity_sense = constrain(configuration.epiano.velocity_sense - ENCODER[ENC_R].speed(), EP_VELOCITY_SENSE_MIN, EP_VELOCITY_SENSE_MAX);
      }
    }

    display_bar_int("EP Vel. Sense", configuration.epiano.velocity_sense, 1.0, EP_VELOCITY_SENSE_MIN, EP_VELOCITY_SENSE_MAX, 3, false, false, false);
    ep.setVelocitySense(mapfloat(configuration.epiano.velocity_sense, EP_VELOCITY_SENSE_MIN, EP_VELOCITY_SENSE_MAX, 0, 1.0));
  }

  if (LCDML.FUNC_close())  // ****** STABLE END *********
  {
    lcd_special_chars(SCROLLBAR);
    encoderDir[ENC_R].reset();
  }
}

void UI_func_epiano_reverb_send(uint8_t param) {
  if (LCDML.FUNC_setup())  // ****** SETUP *********
  {
    encoderDir[ENC_R].reset();

    lcd_special_chars(BLOCKBAR);
    display_bar_int("EP Reverb Send", configuration.fx.ep_reverb_send, 1.0, EP_REVERB_SEND_MIN, EP_REVERB_SEND_MAX, 3, false, false, true);
  }

  if (LCDML.FUNC_loop())  // ****** LOOP *********
  {
    if ((LCDML.BT_checkDown() && encoderDir[ENC_R].Down()) || (LCDML.BT_checkUp() && encoderDir[ENC_R].Up()) || (LCDML.BT_checkEnter() && encoderDir[ENC_R].ButtonShort())) {
      if (LCDML.BT_checkDown()) {
        configuration.fx.ep_reverb_send = constrain(configuration.fx.ep_reverb_send + ENCODER[ENC_R].speed(), EP_REVERB_SEND_MIN, EP_REVERB_SEND_MAX);
        MD_sendControlChange(configuration.epiano.midi_channel, 91, configuration.fx.ep_reverb_send);
      } else if (LCDML.BT_checkUp()) {
        configuration.fx.ep_reverb_send = constrain(configuration.fx.ep_reverb_send - ENCODER[ENC_R].speed(), EP_REVERB_SEND_MIN, EP_REVERB_SEND_MAX);
        MD_sendControlChange(configuration.epiano.midi_channel, 91, configuration.fx.ep_reverb_send);
      }
    }

    display_bar_int("EP Reverb Send", configuration.fx.ep_reverb_send, 1.0, EP_REVERB_SEND_MIN, EP_REVERB_SEND_MAX, 3, false, false, false);

    reverb_mixer_r.gain(REVERB_MIX_CH_EPIANO, volume_transform(mapfloat(configuration.fx.ep_reverb_send, EP_REVERB_SEND_MIN, EP_REVERB_SEND_MAX, 0.0, VOL_MAX_FLOAT)));
    reverb_mixer_l.gain(REVERB_MIX_CH_EPIANO, volume_transform(mapfloat(configuration.fx.ep_reverb_send, EP_REVERB_SEND_MIN, EP_REVERB_SEND_MAX, 0.0, VOL_MAX_FLOAT)));
  }

  if (LCDML.FUNC_close())  // ****** STABLE END *********
  {
    lcd_special_chars(SCROLLBAR);
    encoderDir[ENC_R].reset();
  }
}

void UI_func_epiano_chorus_frequency(uint8_t param) {
  if (LCDML.FUNC_setup())  // ****** SETUP *********
  {
    encoderDir[ENC_R].reset();

    lcd_special_chars(BLOCKBAR);
    display_bar_float("EP Chorus Frq.", configuration.fx.ep_chorus_frequency, 0.1, EP_CHORUS_FREQUENCY_MIN, EP_CHORUS_FREQUENCY_MAX, 2, 1, false, false, true);
  }

  if (LCDML.FUNC_loop())  // ****** LOOP *********
  {
    if ((LCDML.BT_checkDown() && encoderDir[ENC_R].Down()) || (LCDML.BT_checkUp() && encoderDir[ENC_R].Up())) {
      if (LCDML.BT_checkDown())
        configuration.fx.ep_chorus_frequency = constrain(configuration.fx.ep_chorus_frequency + ENCODER[ENC_R].speed(), EP_CHORUS_FREQUENCY_MIN, EP_CHORUS_FREQUENCY_MAX);
      else if (LCDML.BT_checkUp())
        configuration.fx.ep_chorus_frequency = constrain(configuration.fx.ep_chorus_frequency - ENCODER[ENC_R].speed(), EP_CHORUS_FREQUENCY_MIN, EP_CHORUS_FREQUENCY_MAX);
    }
    display_bar_float("EP Chorus Frq.", configuration.fx.ep_chorus_frequency, 0.1, EP_CHORUS_FREQUENCY_MIN, EP_CHORUS_FREQUENCY_MAX, 2, 1, false, false, false);
    ep_chorus_modulator.frequency(configuration.fx.ep_chorus_frequency / 10.0);
  }

  if (LCDML.FUNC_close())  // ****** STABLE END *********
  {
    lcd_special_chars(SCROLLBAR);
    encoderDir[ENC_R].reset();
  }
}

void UI_func_epiano_chorus_waveform(uint8_t param) {
  if (LCDML.FUNC_setup())  // ****** SETUP *********
  {
    encoderDir[ENC_R].reset();

    display.setCursor(0, 0);
    display.print(F("EP Ch. Wavefrm"));
  }

  if (LCDML.FUNC_loop())  // ****** LOOP *********
  {
    if (LCDML.BT_checkDown() && encoderDir[ENC_R].Down())
      configuration.fx.ep_chorus_waveform = constrain(configuration.fx.ep_chorus_waveform + 1, EP_CHORUS_WAVEFORM_MIN, EP_CHORUS_WAVEFORM_MAX);
    else if (LCDML.BT_checkUp() && encoderDir[ENC_R].Up())
      configuration.fx.ep_chorus_waveform = constrain(configuration.fx.ep_chorus_waveform - 1, EP_CHORUS_WAVEFORM_MIN, EP_CHORUS_WAVEFORM_MAX);

    display.setCursor(0, 1);
    switch (configuration.fx.ep_chorus_waveform) {
      case 0:
        ep_chorus_modulator.begin(WAVEFORM_TRIANGLE);
        display.print(F("[TRIANGLE]"));
        break;
      case 1:
        ep_chorus_modulator.begin(WAVEFORM_SINE);
        display.print(F("[SINE    ]"));
        break;
      default:
        ep_chorus_modulator.begin(WAVEFORM_TRIANGLE);
        display.print(F("[TRIANGLE]"));
        break;
    }
  }

  if (LCDML.FUNC_close())  // ****** STABLE END *********
  {
    lcd_special_chars(SCROLLBAR);
    encoderDir[ENC_R].reset();
  }
}

void UI_func_epiano_chorus_depth(uint8_t param) {
  if (LCDML.FUNC_setup())  // ****** SETUP *********
  {
    encoderDir[ENC_R].reset();

    lcd_special_chars(BLOCKBAR);
    display_bar_int("EP Ch. Depth", configuration.fx.ep_chorus_depth, 1.0, EP_CHORUS_DEPTH_MIN, EP_CHORUS_DEPTH_MAX, 3, false, false, true);
  }

  if (LCDML.FUNC_loop())  // ****** LOOP *********
  {
    if ((LCDML.BT_checkDown() && encoderDir[ENC_R].Down()) || (LCDML.BT_checkUp() && encoderDir[ENC_R].Up())) {
      if (LCDML.BT_checkDown())
        configuration.fx.ep_chorus_depth = constrain(configuration.fx.ep_chorus_depth + ENCODER[ENC_R].speed(), EP_CHORUS_DEPTH_MIN, EP_CHORUS_DEPTH_MAX);
      else if (LCDML.BT_checkUp())
        configuration.fx.ep_chorus_depth = constrain(configuration.fx.ep_chorus_depth - ENCODER[ENC_R].speed(), EP_CHORUS_DEPTH_MIN, EP_CHORUS_DEPTH_MAX);
    }

    display_bar_int("EP Ch. Depth", configuration.fx.ep_chorus_depth, 1.0, EP_CHORUS_DEPTH_MIN, EP_CHORUS_DEPTH_MAX, 3, false, false, false);
    ep_chorus_modulator.amplitude(mapfloat(configuration.fx.ep_chorus_depth, EP_CHORUS_DEPTH_MIN, EP_CHORUS_DEPTH_MAX, 0.0, 1.0));
  }

  if (LCDML.FUNC_close())  // ****** STABLE END *********
  {
    lcd_special_chars(SCROLLBAR);
    encoderDir[ENC_R].reset();
  }
}

void UI_func_epiano_chorus_level(uint8_t param) {
  if (LCDML.FUNC_setup())  // ****** SETUP *********
  {
    encoderDir[ENC_R].reset();

    lcd_special_chars(BLOCKBAR);
    display_bar_int("EP Ch. Level", configuration.fx.ep_chorus_level, 1.0, EP_CHORUS_LEVEL_MIN, EP_CHORUS_LEVEL_MAX, 3, false, false, true);
  }

  if (LCDML.FUNC_loop())  // ****** LOOP *********
  {
    if ((LCDML.BT_checkDown() && encoderDir[ENC_R].Down()) || (LCDML.BT_checkUp() && encoderDir[ENC_R].Up())) {
      if (LCDML.BT_checkDown()) {
        configuration.fx.ep_chorus_level = constrain(configuration.fx.ep_chorus_level + ENCODER[ENC_R].speed(), EP_CHORUS_LEVEL_MIN, EP_CHORUS_LEVEL_MAX);
        MD_sendControlChange(configuration.epiano.midi_channel, 93, configuration.fx.ep_chorus_level);
      } else if (LCDML.BT_checkUp()) {
        configuration.fx.ep_chorus_level = constrain(configuration.fx.ep_chorus_level - ENCODER[ENC_R].speed(), EP_CHORUS_LEVEL_MIN, EP_CHORUS_LEVEL_MAX);
        MD_sendControlChange(configuration.epiano.midi_channel, 93, configuration.fx.ep_chorus_level);
      }
    }

    display_bar_int("EP Ch. Level", configuration.fx.ep_chorus_level, 1.0, EP_CHORUS_LEVEL_MIN, EP_CHORUS_LEVEL_MAX, 3, false, false, false);
    ep_chorus_mixer_l.gain(0, 1.0 - mapfloat(configuration.fx.chorus_level[selected_instance_id], CHORUS_LEVEL_MIN, CHORUS_LEVEL_MAX, 0.0, 0.5));
    ep_chorus_mixer_r.gain(0, 1.0 - mapfloat(configuration.fx.chorus_level[selected_instance_id], CHORUS_LEVEL_MIN, CHORUS_LEVEL_MAX, 0.0, 0.5));
  }

  if (LCDML.FUNC_close())  // ****** STABLE END *********
  {
    lcd_special_chars(SCROLLBAR);
    encoderDir[ENC_R].reset();
  }
}

void UI_func_stereo_mono(uint8_t param) {
  static uint8_t old_mono;

  if (LCDML.FUNC_setup())  // ****** SETUP *********
  {
    encoderDir[ENC_R].reset();
    old_mono = configuration.sys.mono;

    display.setCursor(0, 0);
    display.print(F("Stereo/Mono"));
    display.setCursor(0, 1);
    switch (configuration.sys.mono) {
      case 0:
        display.print(F("[STEREO]"));
        stereo2mono.stereo(true);
        break;
      case 1:
        display.print(F("[MONO  ]"));
        stereo2mono.stereo(false);
        break;
      case 2:
        display.print(F("[MONO-R]"));
        stereo2mono.stereo(false);
        break;
      case 3:
        display.print(F("[MONO-L]"));
        stereo2mono.stereo(false);
        break;
    }
  }

  if (LCDML.FUNC_loop())  // ****** LOOP *********
  {
    if (LCDML.BT_checkDown())
      configuration.sys.mono = constrain(configuration.sys.mono + 1, MONO_MIN, MONO_MAX);
    else if (LCDML.BT_checkUp())
      configuration.sys.mono = constrain(configuration.sys.mono - 1, MONO_MIN, MONO_MAX);

    display.setCursor(0, 1);
    switch (configuration.sys.mono) {
      case 0:
        display.print(F("[STEREO]"));
        stereo2mono.stereo(true);
        break;
      case 1:
        display.print(F("[MONO  ]"));
        stereo2mono.stereo(false);
        break;
      case 2:
        display.print(F("[MONO-R]"));
        stereo2mono.stereo(false);
        break;
      case 3:
        display.print(F("[MONO-L]"));
        stereo2mono.stereo(false);
        break;
    }
    set_volume(configuration.sys.vol, configuration.sys.mono);
  }

  if (LCDML.FUNC_close())  // ****** STABLE END *********
  {
    lcd_special_chars(SCROLLBAR);
    encoderDir[ENC_L].reset();

    if (old_mono != configuration.sys.mono) {
      save_sys_flag = true;
      save_sys = 0;
    }
  }
}

void UI_func_polyphony(uint8_t param) {
  if (LCDML.FUNC_setup())  // ****** SETUP *********
  {
    encoderDir[ENC_R].reset();

    lcd_special_chars(BLOCKBAR);
#if NUM_DEXED > 1
    display_bar_int("Polyphony", configuration.dexed[selected_instance_id].polyphony, 1.0, POLYPHONY_MIN, POLYPHONY_MAX - configuration.dexed[(selected_instance_id + 1) % NUM_DEXED].polyphony, 2, false, false, true);
#else
    display_bar_int("Polyphony", configuration.dexed[selected_instance_id].polyphony, 1.0, POLYPHONY_MIN, POLYPHONY_MAX, 2, false, false, true);
#endif
    lcd_active_instance_number(selected_instance_id);
    UI_update_instance_icons();
  }

  if (LCDML.FUNC_loop())  // ****** LOOP *********
  {
    if ((LCDML.BT_checkDown() && encoderDir[ENC_R].Down()) || (LCDML.BT_checkUp() && encoderDir[ENC_R].Up()) || (LCDML.BT_checkEnter() && encoderDir[ENC_R].ButtonShort())) {
      if (LCDML.BT_checkDown()) {
#if NUM_DEXED > 1
        if (configuration.dexed[selected_instance_id].polyphony < POLYPHONY_MAX - configuration.dexed[(selected_instance_id + 1) % NUM_DEXED].polyphony)
          configuration.dexed[selected_instance_id].polyphony = constrain(configuration.dexed[selected_instance_id].polyphony + 1, POLYPHONY_MIN, POLYPHONY_MAX - configuration.dexed[(selected_instance_id + 1) % NUM_DEXED].polyphony);
#else
        configuration.dexed[selected_instance_id].polyphony = constrain(configuration.dexed[selected_instance_id].polyphony + 1, POLYPHONY_MIN, POLYPHONY_MAX);
#endif
      } else if (LCDML.BT_checkUp()) {
        if (configuration.dexed[selected_instance_id].polyphony - 1 < 0)
          configuration.dexed[selected_instance_id].polyphony = 0;
        else {
#if NUM_DEXED > 1
          configuration.dexed[selected_instance_id].polyphony = constrain(configuration.dexed[selected_instance_id].polyphony - 1, POLYPHONY_MIN, POLYPHONY_MAX - configuration.dexed[(selected_instance_id + 1) % NUM_DEXED].polyphony);
#else
          configuration.dexed[selected_instance_id].polyphony = constrain(configuration.dexed[selected_instance_id].polyphony - 1, POLYPHONY_MIN, POLYPHONY_MAX);
#endif
        }
      }
#if NUM_DEXED > 1
      else if (LCDML.BT_checkEnter()) {
        selected_instance_id = !selected_instance_id;
        lcd_active_instance_number(selected_instance_id);
        UI_update_instance_icons();
      }
      lcd_active_instance_number(selected_instance_id);
#endif
    }

#if NUM_DEXED > 1
    display_bar_int("Polyphony", configuration.dexed[selected_instance_id].polyphony, 1.0, POLYPHONY_MIN, POLYPHONY_MAX - configuration.dexed[(selected_instance_id + 1) % NUM_DEXED].polyphony, 2, false, false, false);
#else
    display_bar_int("Polyphony", configuration.dexed[selected_instance_id].polyphony, 1.0, POLYPHONY_MIN, POLYPHONY_MAX, 2, false, false, false);
#endif
    MicroDexed[selected_instance_id]->setMaxNotes(configuration.dexed[selected_instance_id].polyphony);
  }

  if (LCDML.FUNC_close())  // ****** STABLE END *********
  {
    lcd_special_chars(SCROLLBAR);
    encoderDir[ENC_R].reset();
  }
}

void UI_func_mono_poly(uint8_t param) {
  if (LCDML.FUNC_setup())  // ****** SETUP *********
  {
    encoderDir[ENC_R].reset();

    display.setCursor(0, 0);
    display.print(F("Mono/Poly"));

    lcd_active_instance_number(selected_instance_id);
    UI_update_instance_icons();
  }

  if (LCDML.FUNC_loop())  // ****** LOOP *********
  {
    if ((LCDML.BT_checkDown() && encoderDir[ENC_R].Down()) || (LCDML.BT_checkUp() && encoderDir[ENC_R].Up())) {
      if (LCDML.BT_checkDown())
        configuration.dexed[selected_instance_id].monopoly = constrain(configuration.dexed[selected_instance_id].monopoly + 1, MONOPOLY_MIN, MONOPOLY_MAX);
      else if (LCDML.BT_checkUp())
        configuration.dexed[selected_instance_id].monopoly = constrain(configuration.dexed[selected_instance_id].monopoly - 1, MONOPOLY_MIN, MONOPOLY_MAX);

      MicroDexed[selected_instance_id]->setMonoMode(!configuration.dexed[selected_instance_id].monopoly);
      configuration.dexed[selected_instance_id].monopoly = MicroDexed[selected_instance_id]->getMonoMode();
    }
#if NUM_DEXED > 1
    if (LCDML.BT_checkEnter() && encoderDir[ENC_R].ButtonShort()) {
      selected_instance_id = !selected_instance_id;
      lcd_active_instance_number(selected_instance_id);
      UI_update_instance_icons();
    }
    lcd_active_instance_number(selected_instance_id);
#endif
  }

  display.setCursor(0, 1);
  switch (configuration.dexed[selected_instance_id].monopoly) {
    case 1:
      display.print(F("[MONOPHONIC]"));
      break;
    case 0:
      display.print(F("[POLYPHONIC]"));
      break;
  }

  if (LCDML.FUNC_close())  // ****** STABLE END *********
  {
    lcd_special_chars(SCROLLBAR);
    encoderDir[ENC_R].reset();
  }
}

void UI_func_note_refresh(uint8_t param) {
  if (LCDML.FUNC_setup())  // ****** SETUP *********
  {
    encoderDir[ENC_R].reset();

    display.setCursor(0, 0);
    display.print(F("Note Refresh"));

    lcd_active_instance_number(selected_instance_id);
    UI_update_instance_icons();
  }

  if (LCDML.FUNC_loop())  // ****** LOOP *********
  {
    if ((LCDML.BT_checkDown() && encoderDir[ENC_R].Down()) || (LCDML.BT_checkUp() && encoderDir[ENC_R].Up()) || (LCDML.BT_checkEnter() && encoderDir[ENC_R].ButtonShort())) {
      if (LCDML.BT_checkDown())
        configuration.dexed[selected_instance_id].note_refresh = constrain(configuration.dexed[selected_instance_id].note_refresh + 1, NOTE_REFRESH_MIN, NOTE_REFRESH_MAX);
      else if (LCDML.BT_checkUp())
        configuration.dexed[selected_instance_id].note_refresh = constrain(configuration.dexed[selected_instance_id].note_refresh - 1, NOTE_REFRESH_MIN, NOTE_REFRESH_MAX);
#if NUM_DEXED > 1
      else if (LCDML.BT_checkEnter()) {
        selected_instance_id = !selected_instance_id;
        lcd_active_instance_number(selected_instance_id);
        UI_update_instance_icons();
      }
#endif
    }

    MicroDexed[selected_instance_id]->setNoteRefreshMode(configuration.dexed[selected_instance_id].note_refresh);
#ifdef DEBUG
    Serial.printf_P(PSTR("Note refresh: %d\n"), configuration.dexed[selected_instance_id].note_refresh);
#endif

    display.setCursor(0, 1);
    switch (configuration.dexed[selected_instance_id].note_refresh) {
      case 0:
        display.print(F("[NORMAL     ]"));
        break;
      case 1:
        display.print(F("[RETRIGGERED]"));
        break;
    }
  }

  if (LCDML.FUNC_close())  // ****** STABLE END *********
  {
    lcd_special_chars(SCROLLBAR);
    encoderDir[ENC_R].reset();
  }
}

void UI_func_pb_range(uint8_t param) {
  if (LCDML.FUNC_setup())  // ****** SETUP *********
  {
    encoderDir[ENC_R].reset();

    lcd_special_chars(BLOCKBAR);
    display_bar_int("PB Range", configuration.dexed[selected_instance_id].pb_range, 1.0, PB_RANGE_MIN, PB_RANGE_MAX, 2, false, false, true);

    lcd_active_instance_number(selected_instance_id);
    UI_update_instance_icons();
  }

  if (LCDML.FUNC_loop())  // ****** LOOP *********
  {
    if ((LCDML.BT_checkDown() && encoderDir[ENC_R].Down()) || (LCDML.BT_checkUp() && encoderDir[ENC_R].Up()) || (LCDML.BT_checkEnter() && encoderDir[ENC_R].ButtonShort())) {
      if (LCDML.BT_checkDown())
        configuration.dexed[selected_instance_id].pb_range = constrain(configuration.dexed[selected_instance_id].pb_range + ENCODER[ENC_R].speed(), PB_RANGE_MIN, PB_RANGE_MAX);
      else if (LCDML.BT_checkUp())
        configuration.dexed[selected_instance_id].pb_range = constrain(configuration.dexed[selected_instance_id].pb_range - ENCODER[ENC_R].speed(), PB_RANGE_MIN, PB_RANGE_MAX);
#if NUM_DEXED > 1
      else if (LCDML.BT_checkEnter()) {
        selected_instance_id = !selected_instance_id;
        lcd_active_instance_number(selected_instance_id);
        UI_update_instance_icons();
      }
#endif
    }

    display_bar_int("PB Range", configuration.dexed[selected_instance_id].pb_range, 1.0, PB_RANGE_MIN, PB_RANGE_MAX, 2, false, false, false);

    MicroDexed[selected_instance_id]->setPBController(configuration.dexed[selected_instance_id].pb_range, configuration.dexed[selected_instance_id].pb_step);
    send_sysex_param(configuration.dexed[selected_instance_id].midi_channel, 65, configuration.dexed[selected_instance_id].pb_range, 2);
  }

  if (LCDML.FUNC_close())  // ****** STABLE END *********
  {
    lcd_special_chars(SCROLLBAR);
    encoderDir[ENC_R].reset();
  }
}

void UI_func_pb_step(uint8_t param) {
  if (LCDML.FUNC_setup())  // ****** SETUP *********
  {
    encoderDir[ENC_R].reset();

    lcd_special_chars(BLOCKBAR);
    display_bar_int("PB Step", configuration.dexed[selected_instance_id].pb_step, 1.0, PB_STEP_MIN, PB_STEP_MAX, 2, false, false, true);

    lcd_active_instance_number(selected_instance_id);
    UI_update_instance_icons();
  }

  if (LCDML.FUNC_loop())  // ****** LOOP *********
  {
    if ((LCDML.BT_checkDown() && encoderDir[ENC_R].Down()) || (LCDML.BT_checkUp() && encoderDir[ENC_R].Up()) || (LCDML.BT_checkEnter() && encoderDir[ENC_R].ButtonShort())) {
      if (LCDML.BT_checkDown())
        configuration.dexed[selected_instance_id].pb_step = constrain(configuration.dexed[selected_instance_id].pb_step + ENCODER[ENC_R].speed(), PB_STEP_MIN, PB_STEP_MAX);
      else if (LCDML.BT_checkUp())
        configuration.dexed[selected_instance_id].pb_step = constrain(configuration.dexed[selected_instance_id].pb_step - ENCODER[ENC_R].speed(), PB_STEP_MIN, PB_STEP_MAX);
#if NUM_DEXED > 1
      else if (LCDML.BT_checkEnter()) {
        selected_instance_id = !selected_instance_id;
        lcd_active_instance_number(selected_instance_id);
        UI_update_instance_icons();
      }
#endif
    }

    display_bar_int("PB Step", configuration.dexed[selected_instance_id].pb_step, 1.0, PB_STEP_MIN, PB_STEP_MAX, 2, false, false, false);

    MicroDexed[selected_instance_id]->setPBController(configuration.dexed[selected_instance_id].pb_range, configuration.dexed[selected_instance_id].pb_step);
    send_sysex_param(configuration.dexed[selected_instance_id].midi_channel, 66, configuration.dexed[selected_instance_id].pb_step, 2);
  }

  if (LCDML.FUNC_close())  // ****** STABLE END *********
  {
    lcd_special_chars(SCROLLBAR);
    encoderDir[ENC_R].reset();
  }
}
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
